MaxVinzens/Cocktail-Mix-Maschine-V2/Doku/Sauber zauber.pdf

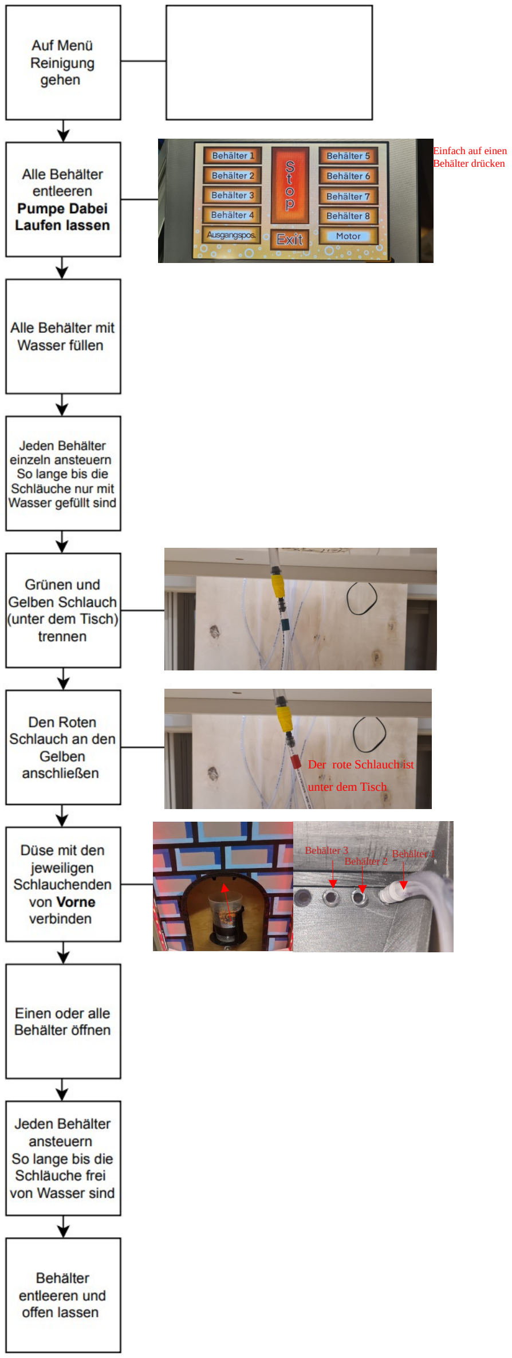
[picture p28: page 1]

Einfach auf einen
Behälter drücken

Behälter 1
Behälter 2

Behälter 3

Der rote Schlauch ist
unter dem Tisch
