MaxVinzens/Cocktail-Mix-Maschine-V2/Konzepte/Saubermachen/Drawing1.pdf

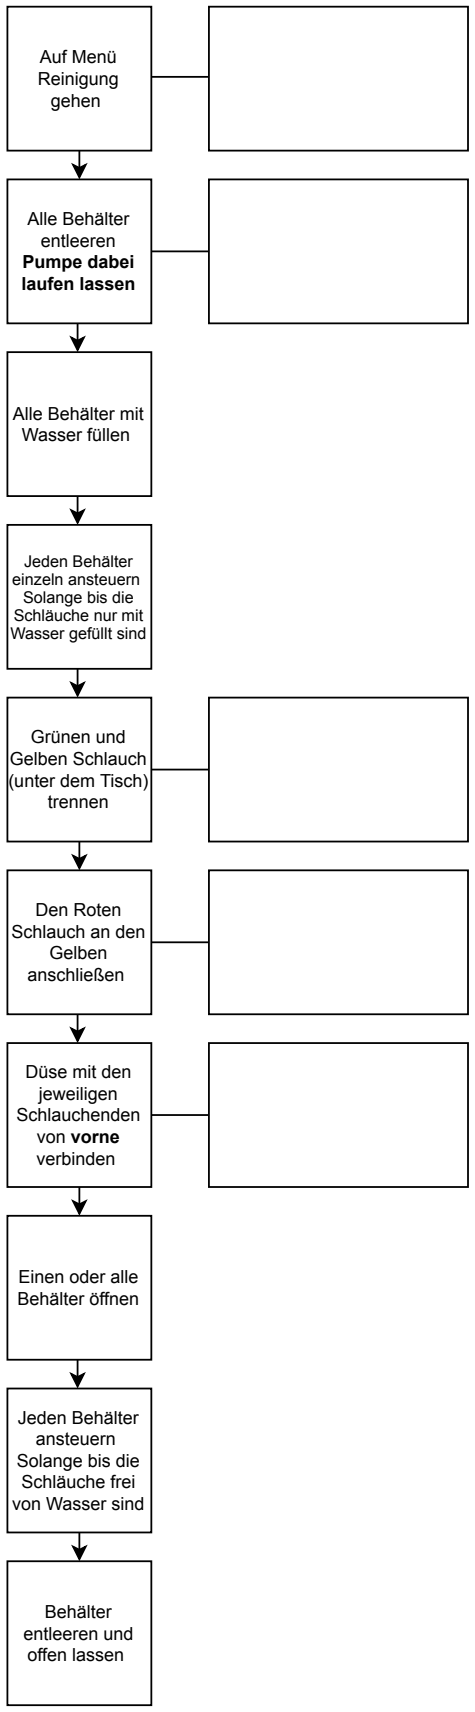
[picture p29: figure]
Auf Menü Reinigung gehen; Alle Behälter entleeren Pumpe dabei laufen lassen; Alle Behälter mit Wasser füllen; Jeden Behälter einzeln ansteuern Solange bis die Schläuche nur mit Wasser gefüllt sind; Grünen und Gelben Schlauch (unter dem Tisch) trennen; Den Roten Schlauch an den Gelben anschließen; Düse mit den jeweiligen Schlauchenden von vorne verbinden; Einen oder alle Behälter öffnen; Jeden Behälter ansteuern Solange bis die Schläuche frei von Wasser sind; Behälter entleeren und offen lassen
