MaxVinzens/Cocktail-Mix-Maschine-V2/Bildschirm Menüs/IMG_2407.jpeg

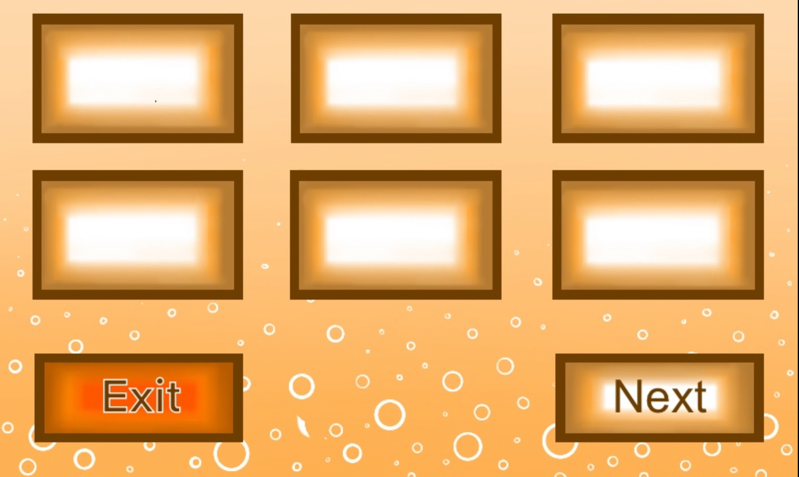
Bildschirm Menüs/IMG_2407.jpeg
