MaxVinzens/Cocktail-Mix-Maschine-V2/Code für SPS/Logical/mappView/Resources/Media/Cocktail.JPG

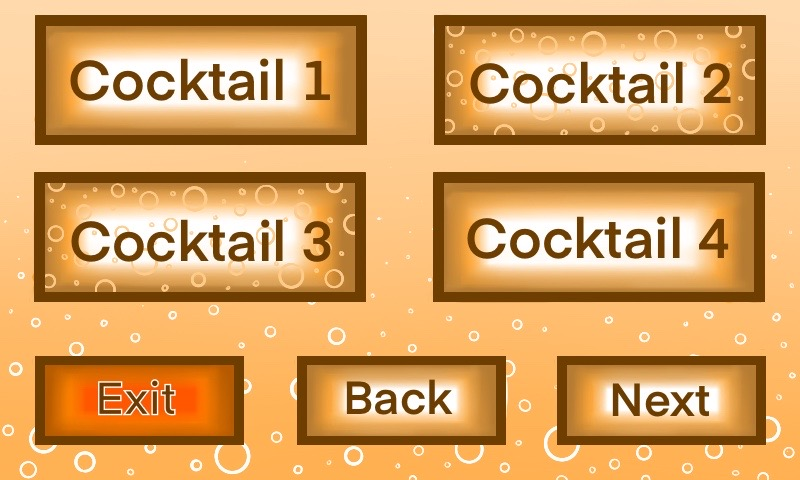
Code für SPS/Logical/mappView/Resources/Media/Cocktail.JPG
