MaxVinzens/Cocktail-Mix-Maschine-V2/Code für SPS/Logical/mappView/Resources/Media/Eis_Groesse.jpg

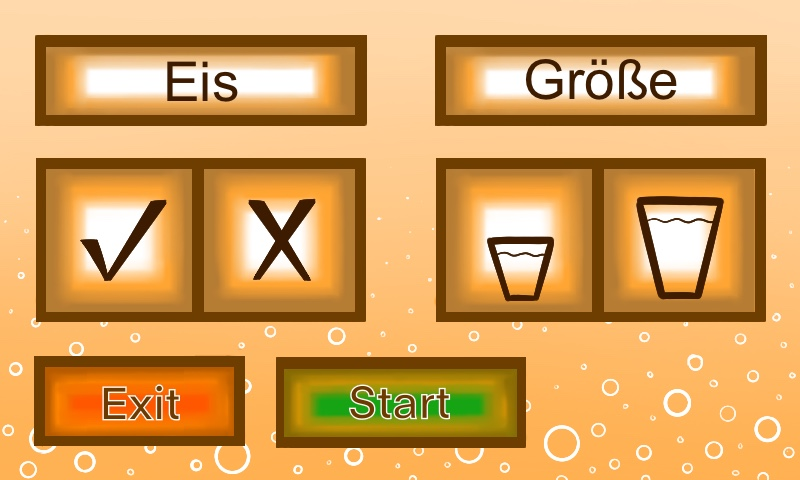
Code für SPS/Logical/mappView/Resources/Media/Eis_Groesse.jpg
