MaxVinzens/Cocktail-Mix-Maschine-V2/Code für SPS/Logical/mappView/Resources/Media/Hauptbildschirm.jpg

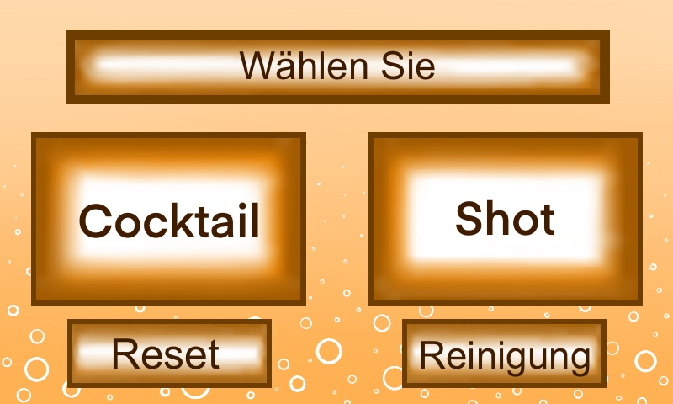
Code für SPS/Logical/mappView/Resources/Media/Hauptbildschirm.jpg
