MaxVinzens/Cocktail-Mix-Maschine-V2/Code für SPS/Logical/mappView/Resources/Media/Reinigung_final.jpg

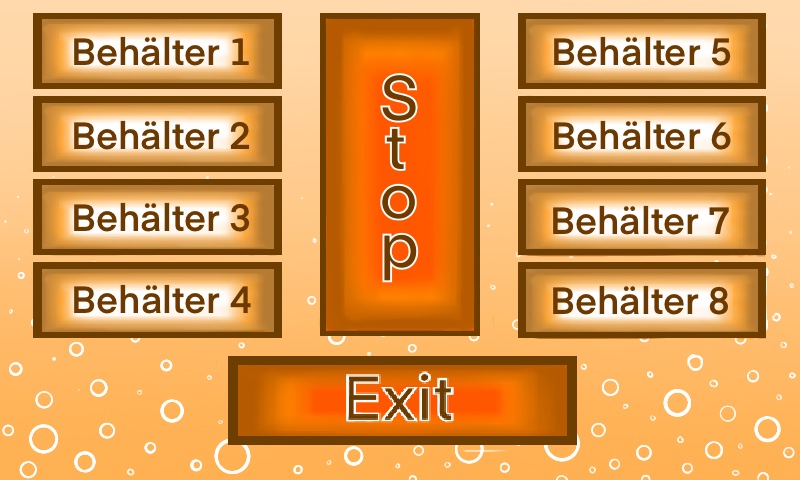
Code für SPS/Logical/mappView/Resources/Media/Reinigung_final.jpg
