MaxVinzens/Cocktail-Mix-Maschine-V2/Code für SPS/Logical/mappView/Resources/Media/Shot.jpg

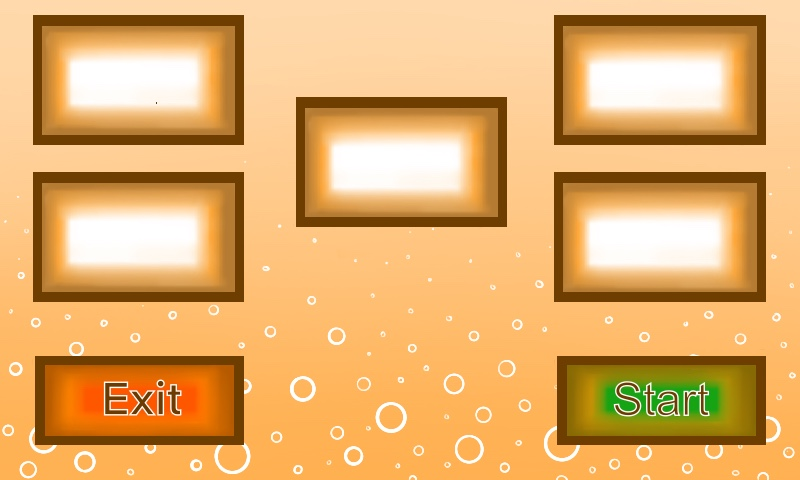
Code für SPS/Logical/mappView/Resources/Media/Shot.jpg
