MaxVinzens/Cocktail-Mix-Maschine-V2/Code für SPS/Logical/mappView/Resources/Media/Startseite.jpg

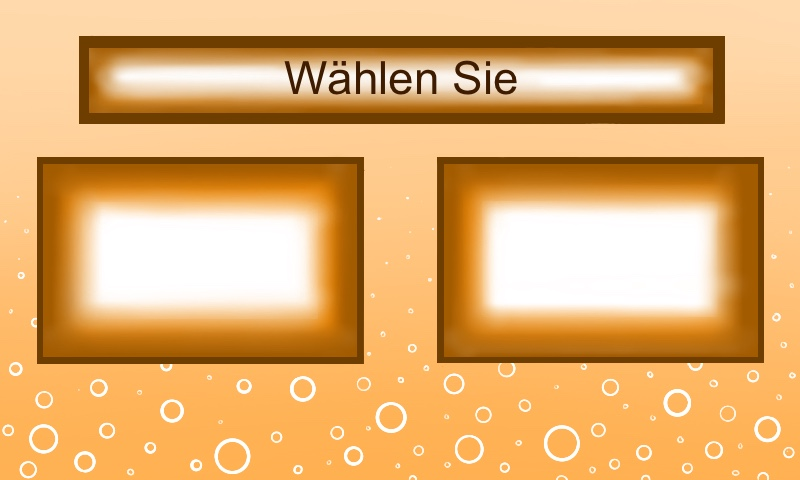
Code für SPS/Logical/mappView/Resources/Media/Startseite.jpg
