MaxVinzens/Cocktail-Mix-Maschine-V2/Code für SPS/Logical/mappView/Resources/Media/Startseite_neu.jpg

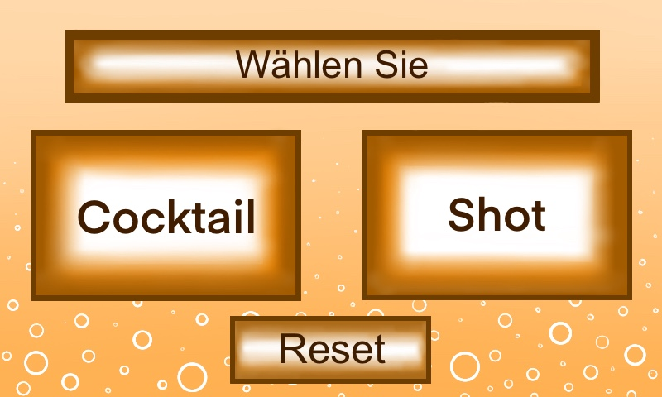
Code für SPS/Logical/mappView/Resources/Media/Startseite_neu.jpg
