MaxVinzens/Cocktail-Mix-Maschine-V2/Doku/Abb.10_Grundskelett_mit_Wägezelle.jpg

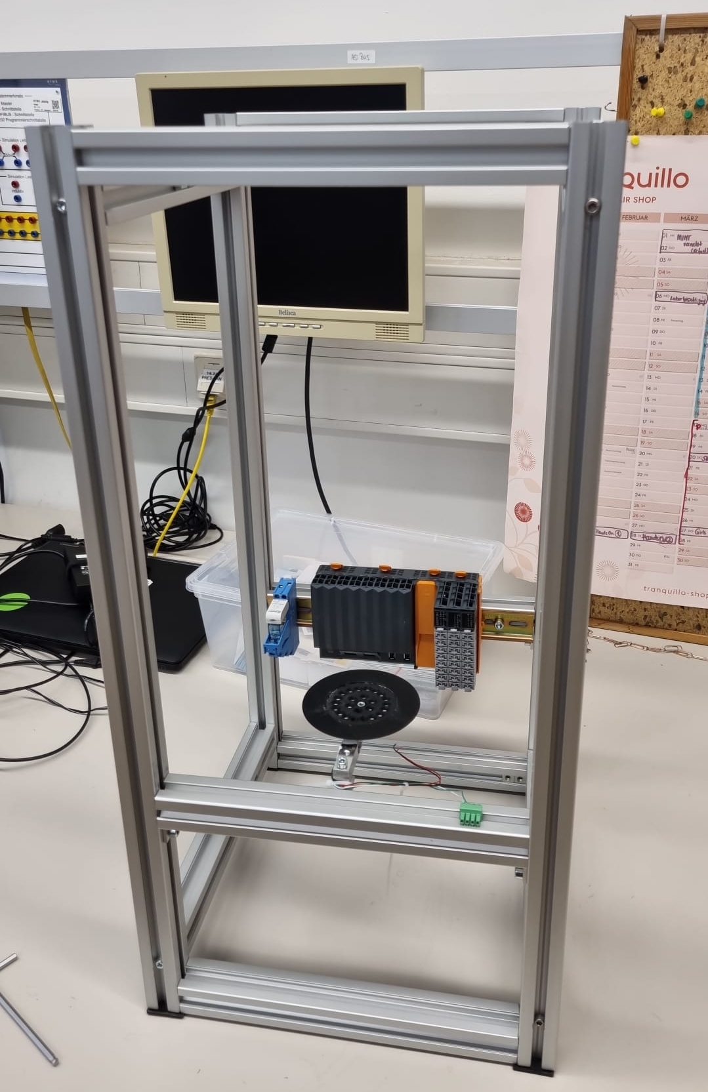
Doku/Abb.10_Grundskelett_mit_Wägezelle.jpg
