MaxVinzens/Cocktail-Mix-Maschine-V2/Fusion/Becherhalter/Für Max (nix ändern)/Schraube.PNG

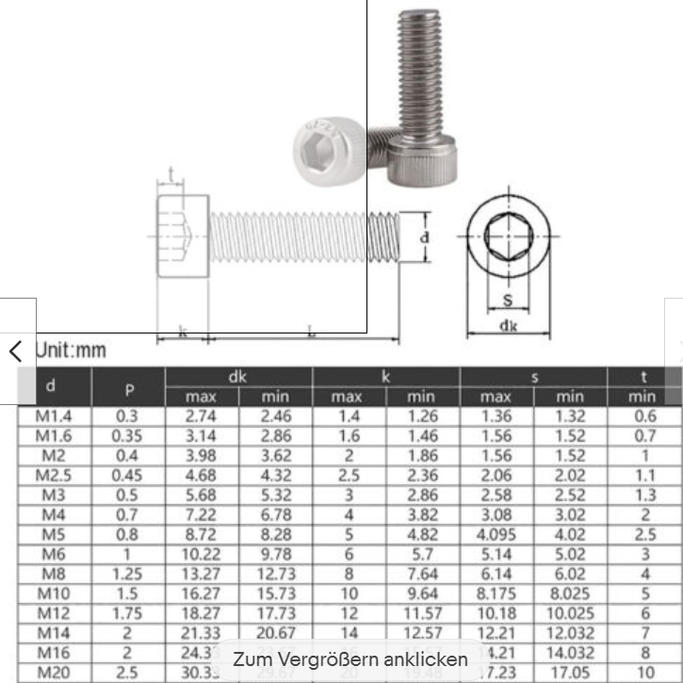
Fusion/Becherhalter/Für Max (nix ändern)/Schraube.PNG
