MaxVinzens/Cocktail-Mix-Maschine-V2/Konzepte/Aussehen/Zeichnung.jpeg

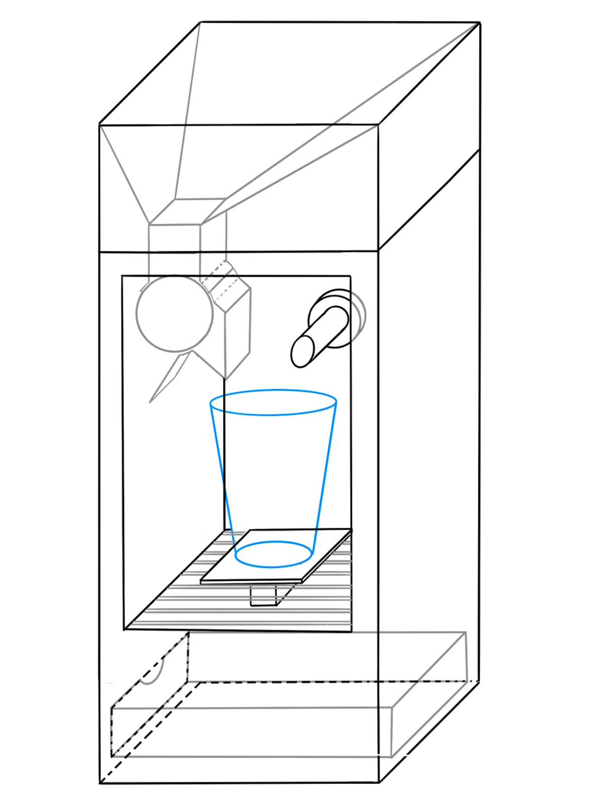
Konzepte/Aussehen/Zeichnung.jpeg
