MaxVinzens/Cocktail-Mix-Maschine-V2/Konzepte/Bildschirm/WhatsApp Image 2023-05-01 at 21.39.04 (1).jpeg

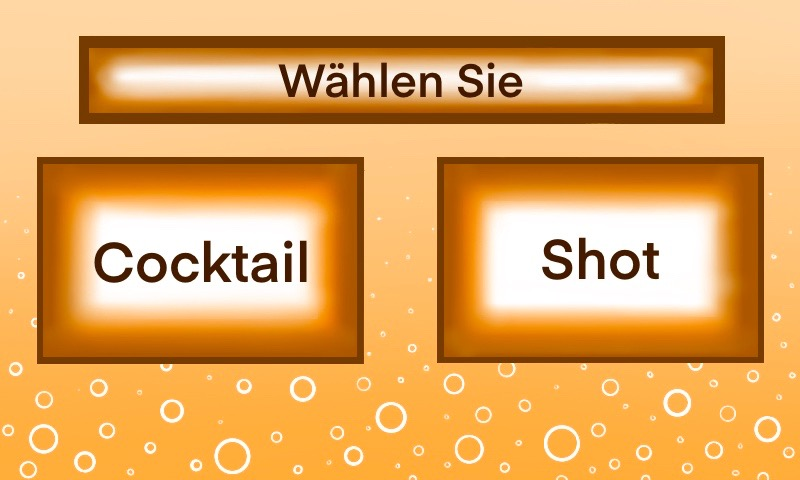
Konzepte/Bildschirm/WhatsApp Image 2023-05-01 at 21.39.04 (1).jpeg
