MaxVinzens/Cocktail-Mix-Maschine-V2/Konzepte/Bildschirm/WhatsApp Image 2023-05-01 at 21.39.05.jpeg

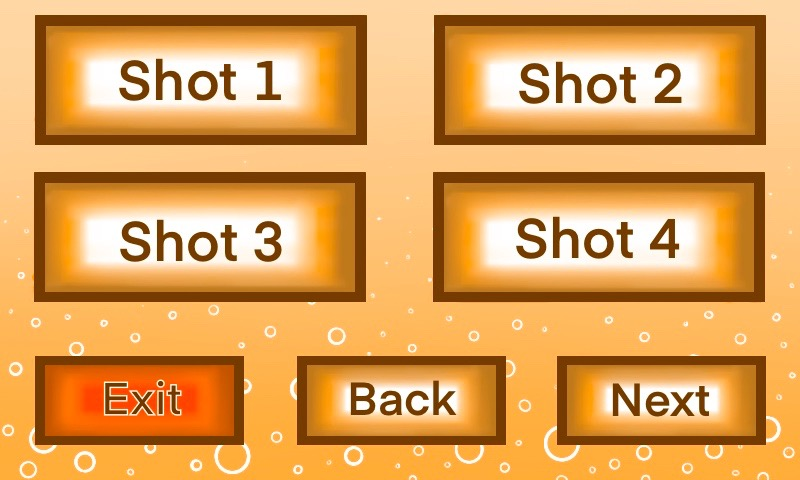
Konzepte/Bildschirm/WhatsApp Image 2023-05-01 at 21.39.05.jpeg
