MaxVinzens/Cocktail-Mix-Maschine-V2/Konzepte/Drinks/drinks1.jpeg

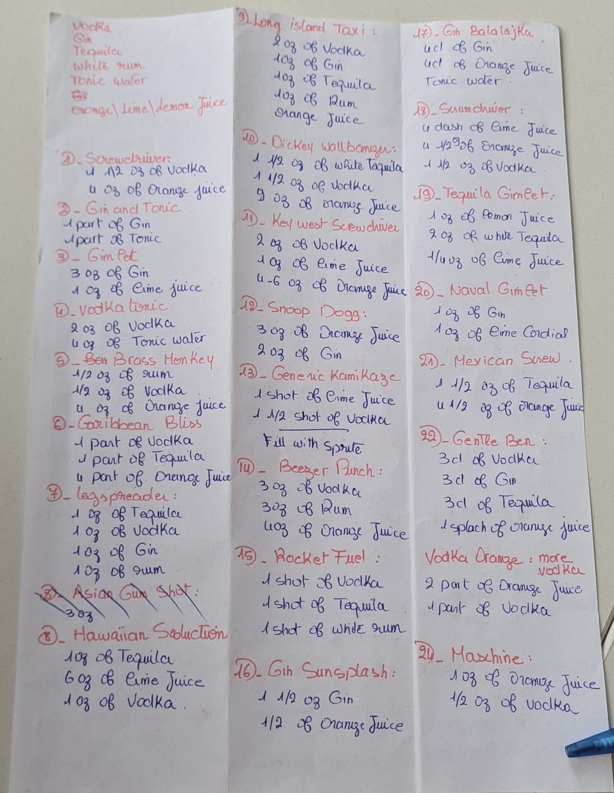
Konzepte/Drinks/drinks1.jpeg
