MaxVinzens/Cocktail-Mix-Maschine-V2/Konzepte/Drinks/Drinks2.jpeg

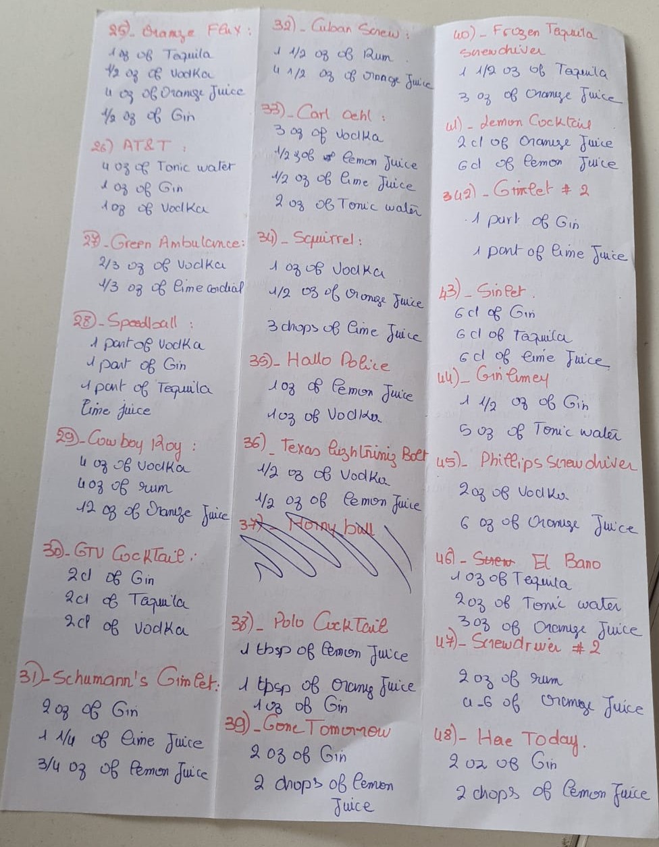
Konzepte/Drinks/Drinks2.jpeg
