MaxVinzens/Cocktail-Mix-Maschine-V2/Reinigung/altes/1.jpg

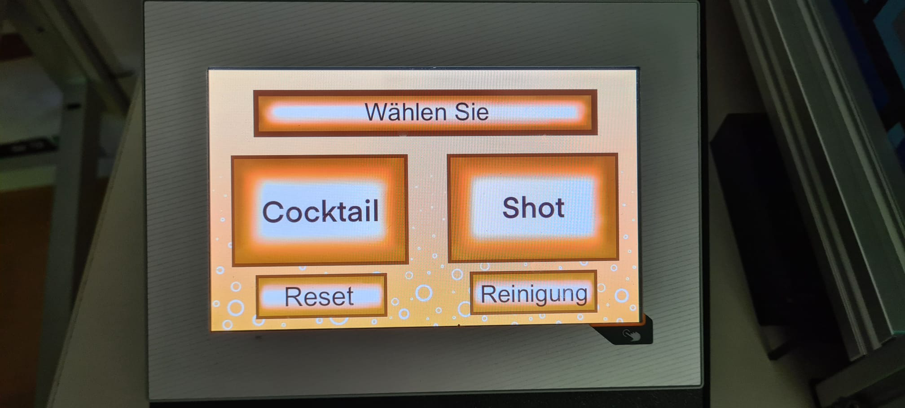
Reinigung/altes/1.jpg
