MaxVinzens/Cocktail-Mix-Maschine-V2/Reinigung/altes/2..jpg

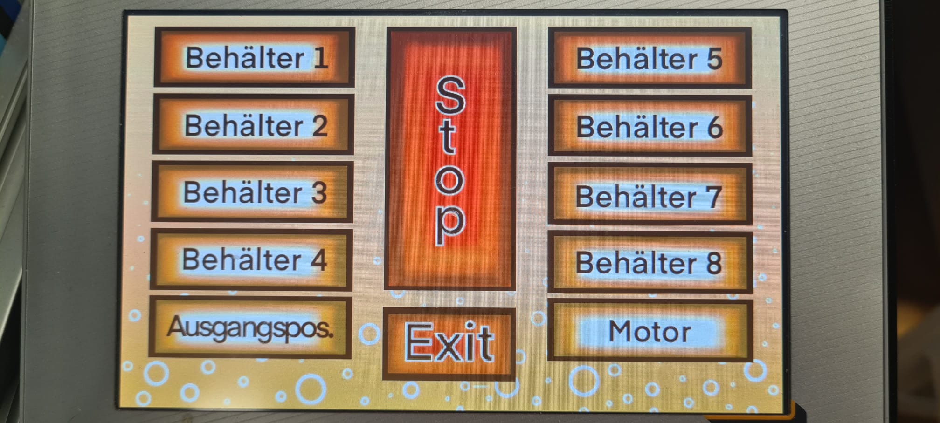
Reinigung/altes/2..jpg
