MaxVinzens/Cocktail-Mix-Maschine-V2/Reinigung/altes/3..jpg

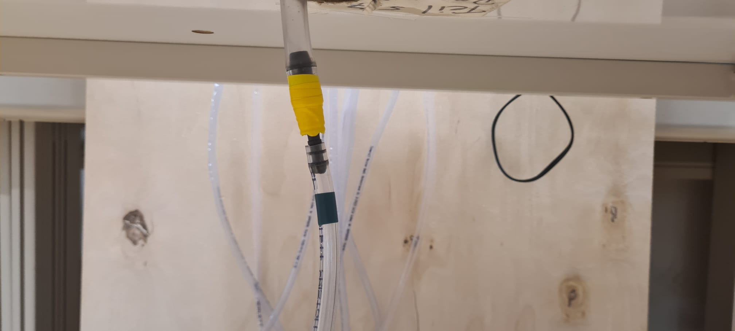
Reinigung/altes/3..jpg
