MaxVinzens/Cocktail-Mix-Maschine-V2/Reinigung/altes/4..jpg

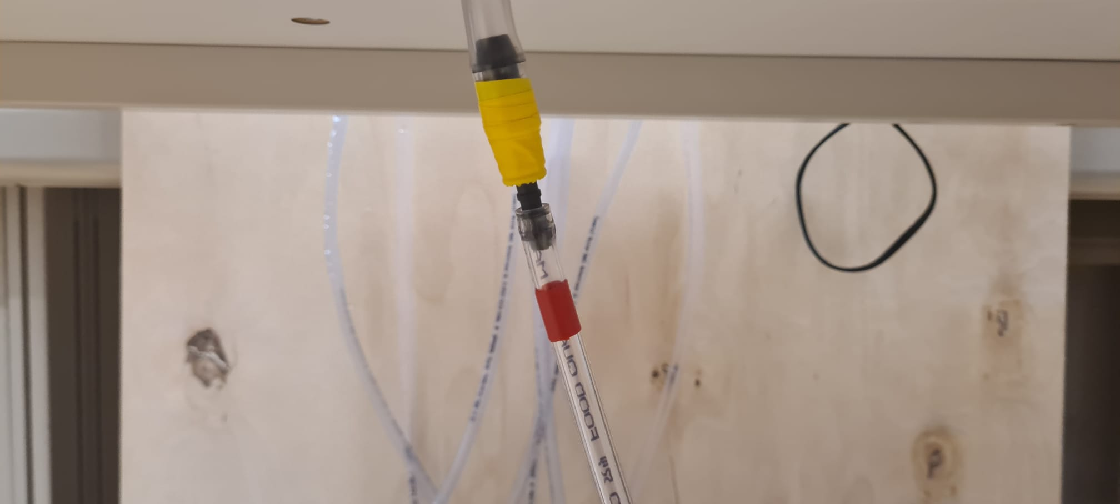
Reinigung/altes/4..jpg
