MaxVinzens/Cocktail-Mix-Maschine-V2/Reinigung/altes/5..jpg

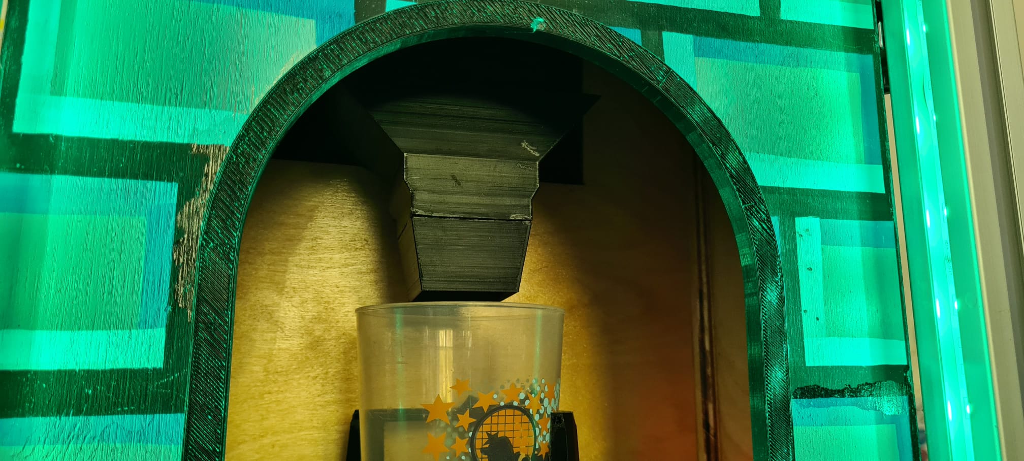
Reinigung/altes/5..jpg
