MaxVinzens/Cocktail-Mix-Maschine-V2/Reinigung/altes/6..jpg

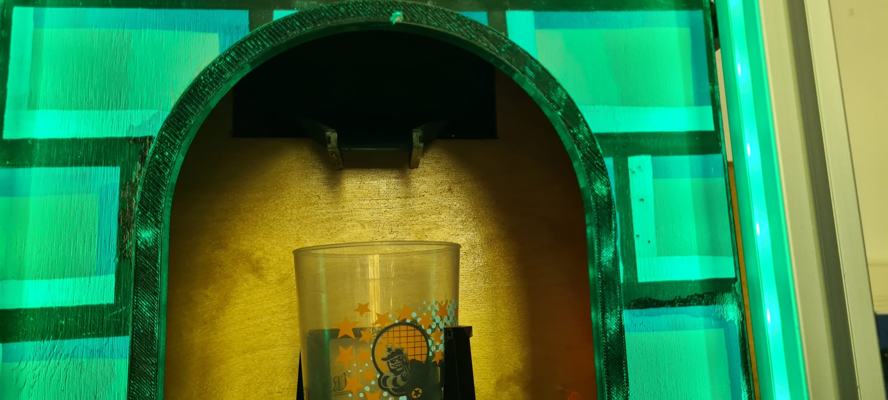
Reinigung/altes/6..jpg
