MaxVinzens/Cocktail-Mix-Maschine-V2/Reinigung/altes/Sauber zauber Bild.PNG

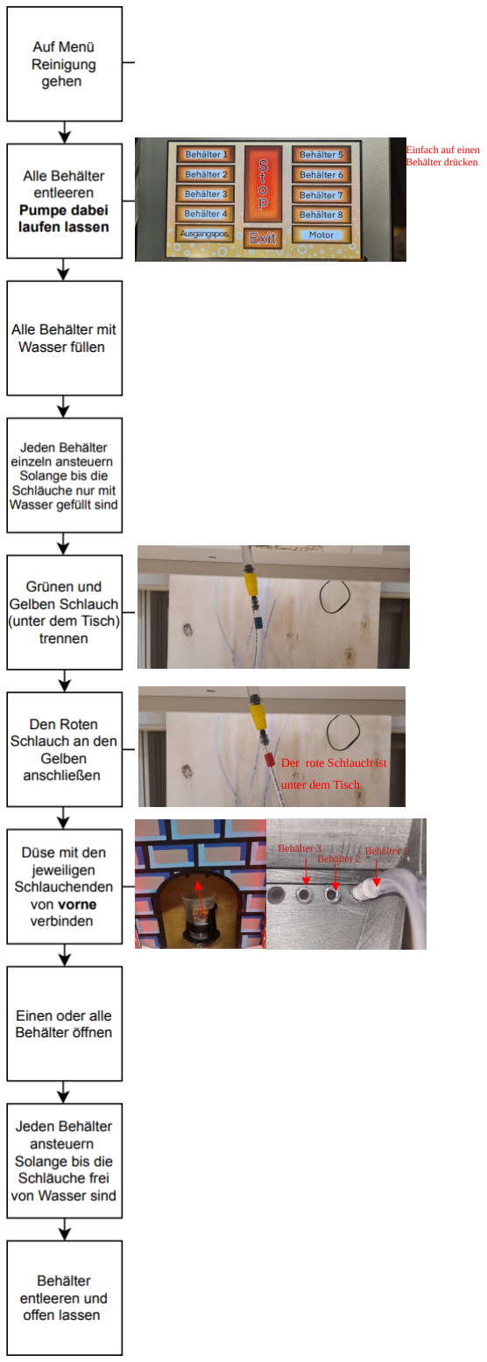
Reinigung/altes/Sauber zauber Bild.PNG
