MaxVinzens/Cocktail-Mix-Maschine-V2/Fusion/Verkleidung/Altes/Abdeckung Profielschiene oben v1.stl

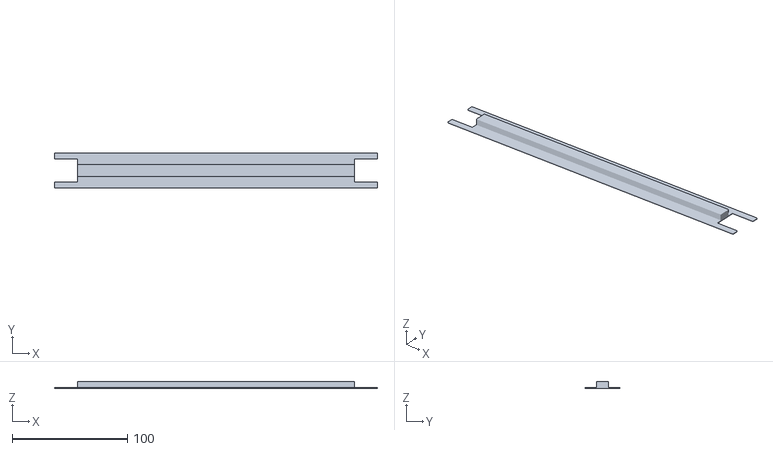
[picture p70: CAD file, 2023-09-12]
Fusion/Verkleidung/Altes/Abdeckung Profielschiene oben v1.stl
280.0 x 30.0 x 6.00
