MaxVinzens/Cocktail-Mix-Maschine-V2/Fusion/Auffangbecken/Halterung Behätler.stl

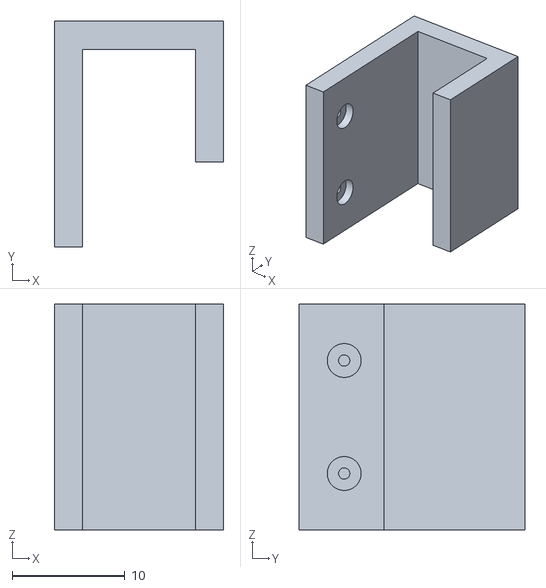
[picture p71: CAD file, 2023-09-09]
Fusion/Auffangbecken/Halterung Behätler.stl
15.0 x 20.0 x 20.0
