MaxVinzens/Cocktail-Mix-Maschine-V2/Fusion/Becherhalter/becherhalter V3 v2.stl

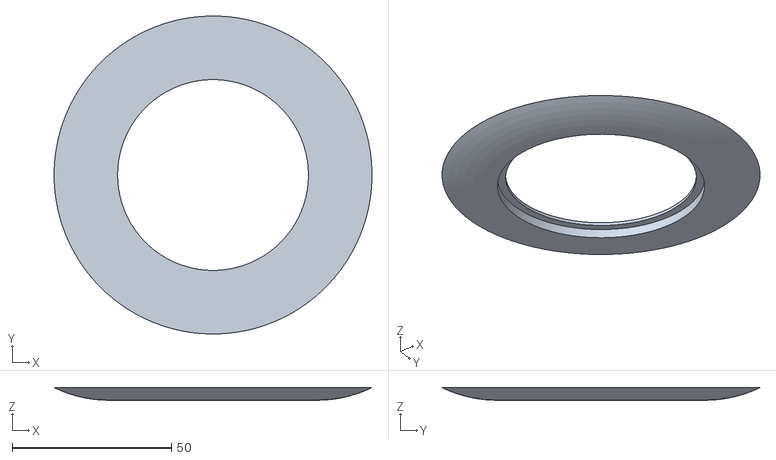
[picture p72: CAD file, 2023-05-09]
Fusion/Becherhalter/becherhalter V3 v2.stl
100.0 x 100.0 x 4.00
