MaxVinzens/Cocktail-Mix-Maschine-V2/Fusion/Eisdosierer/getriebe.FCStd

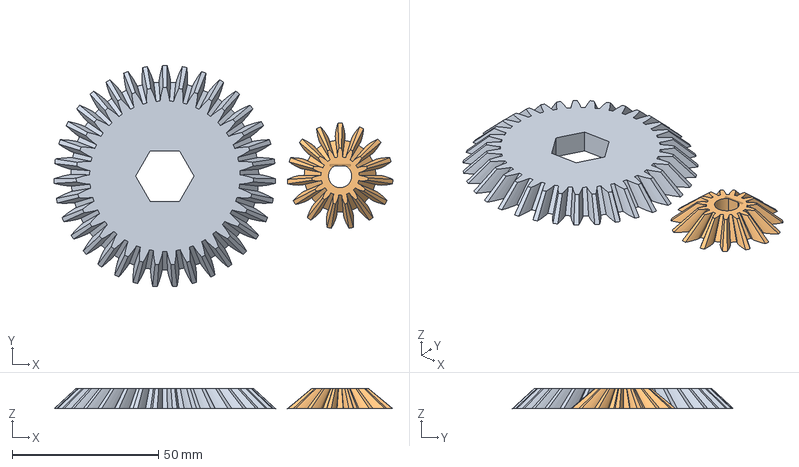
[picture p73: CAD file, 2023-09-13]
Fusion/Eisdosierer/getriebe.FCStd
116.0 x 75.8 x 7.00 mm
Zahnrad Eisdosierer
zahnrad motor
