MaxVinzens/Cocktail-Mix-Maschine-V2/Fusion/Verkleidung/Verkleidung.stl

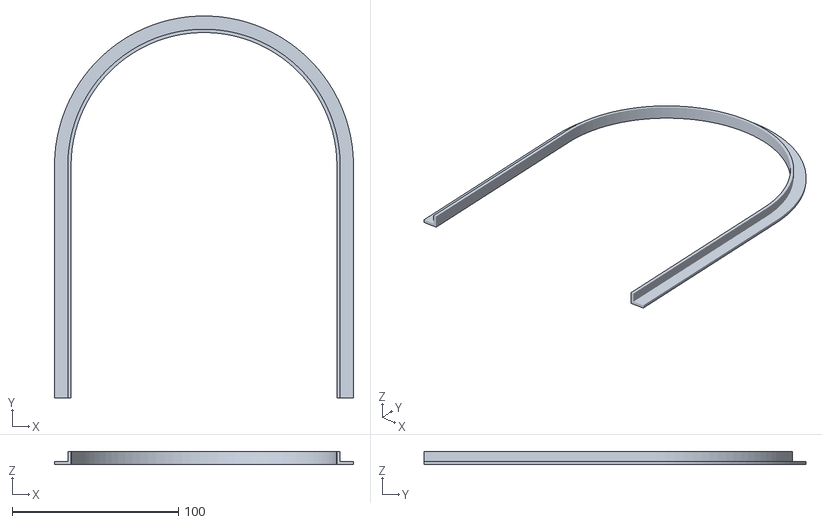
[picture p74: CAD file, 2023-09-10]
Fusion/Verkleidung/Verkleidung.stl
180.0 x 230.0 x 8.00
