MaxVinzens/Cocktail-Mix-Maschine-V2/Fusion/Eisdosierer/Spritzschutz_Schiene-Body.stl

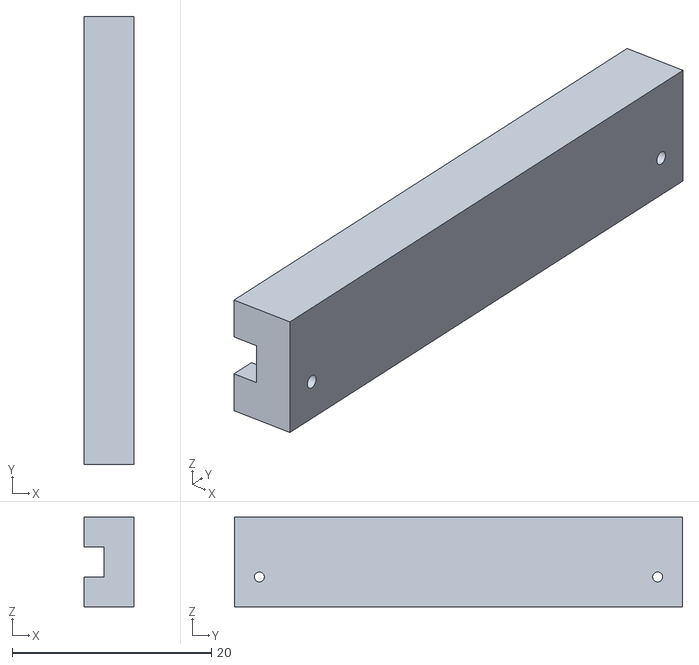
[picture p75: CAD file, 2023-09-13]
Fusion/Eisdosierer/Spritzschutz_Schiene-Body.stl
5.00 x 45.0 x 9.00
