MaxVinzens/Cocktail-Mix-Maschine-V2/Fusion/Eisdosierer/trichter_Ausgang4-Seite1.stl

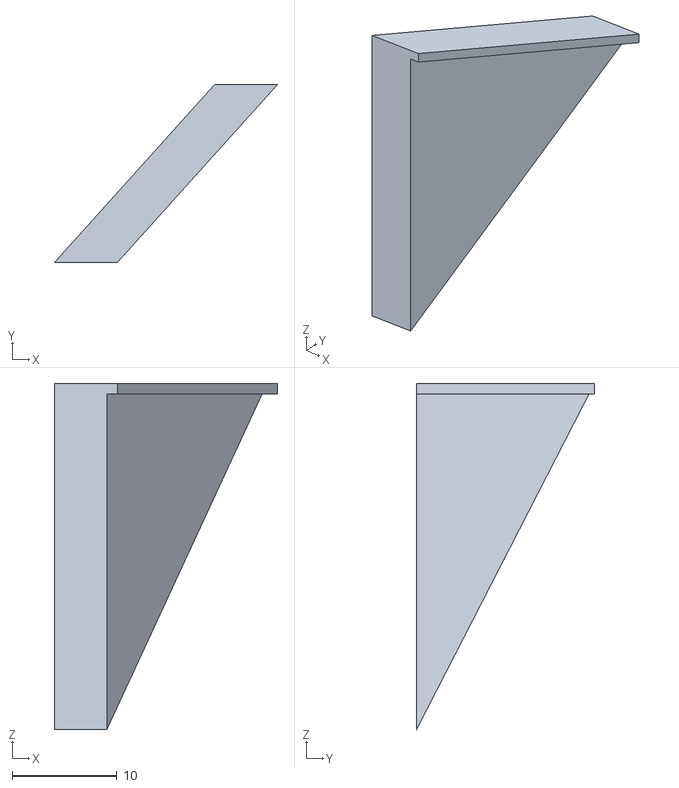
[picture p76: CAD file, 2023-09-13]
Fusion/Eisdosierer/trichter_Ausgang4-Seite1.stl
21.3 x 17.0 x 33.0
