MaxVinzens/Cocktail-Mix-Maschine-V2/Fusion/Eisdosierer/Eisdosierer_walze2.FCStd

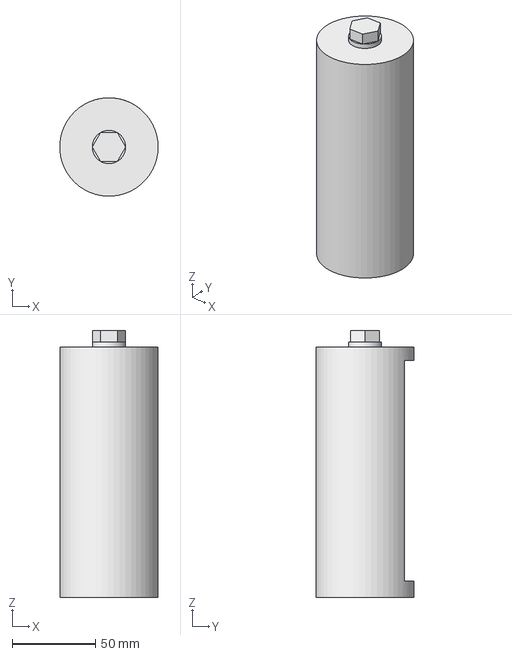
[picture p77: CAD file, 2023-09-13]
Fusion/Eisdosierer/Eisdosierer_walze2.FCStd
58.9 x 59.0 x 160.0 mm
