MaxVinzens/Cocktail-Mix-Maschine-V2/Fusion/Eisdosierer/trichter_Ausgang4.FCStd

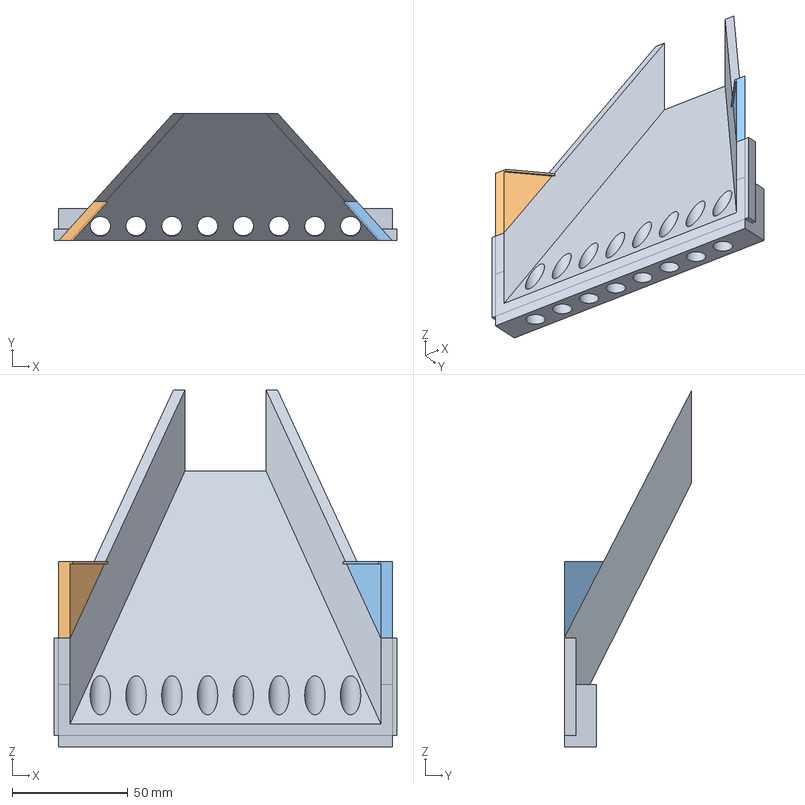
[picture p78: CAD file, 2023-09-13]
Fusion/Eisdosierer/trichter_Ausgang4.FCStd
148.0 x 55.0 x 154.0 mm
Seite1
Seite2
