MaxVinzens/Cocktail-Mix-Maschine-V2/Fusion/Eisdosierer/Spritzschutz-Teil2.stl

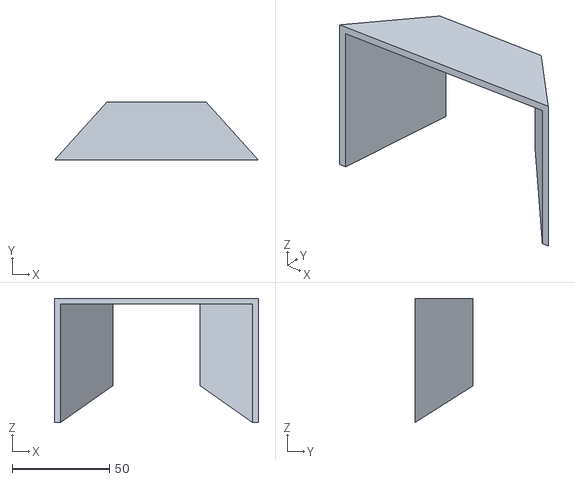
[picture p79: CAD file, 2023-09-13]
Fusion/Eisdosierer/Spritzschutz-Teil2.stl
105.0 x 30.0 x 64.0
