MaxVinzens/Cocktail-Mix-Maschine-V2/Fusion/Eisdosierer/Platte_mitloch.FCStd

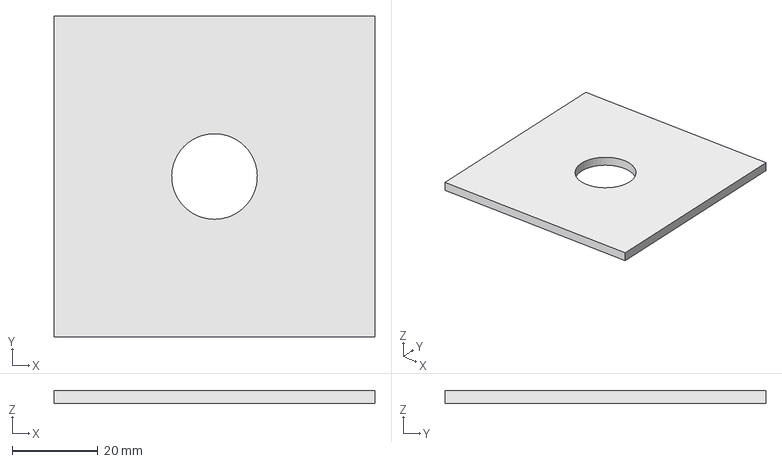
[picture p80: CAD file, 2023-09-13]
Fusion/Eisdosierer/Platte_mitloch.FCStd
75.0 x 75.0 x 3.00 mm
