MaxVinzens/Cocktail-Mix-Maschine-V2/Fusion/Eisdosierer/Eisdosierer1.FCStd

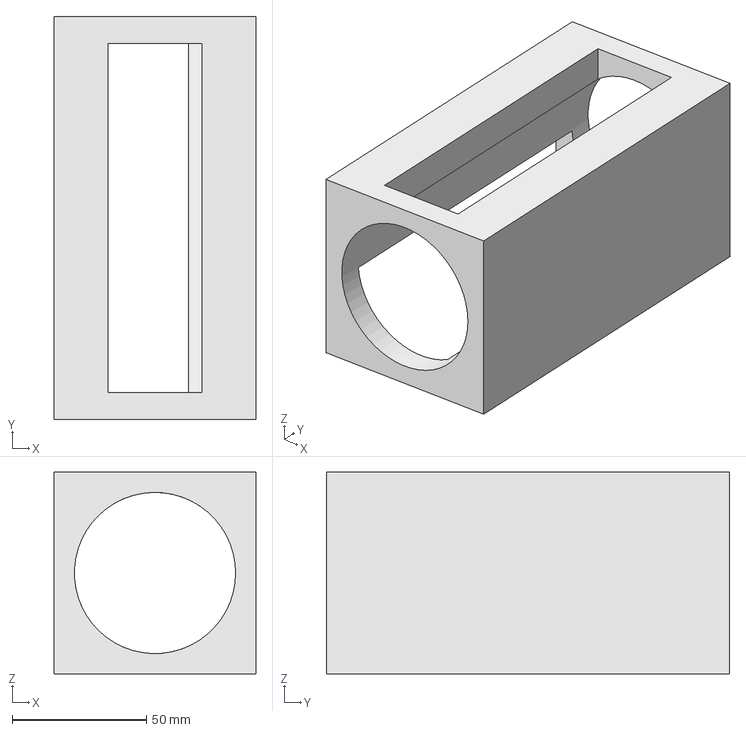
[picture p81: CAD file, 2023-09-13]
Fusion/Eisdosierer/Eisdosierer1.FCStd
75.0 x 150.0 x 75.0 mm
