MaxVinzens/Cocktail-Mix-Maschine-V2/Fusion/Eisdosierer/Spritzschutz.FCStd

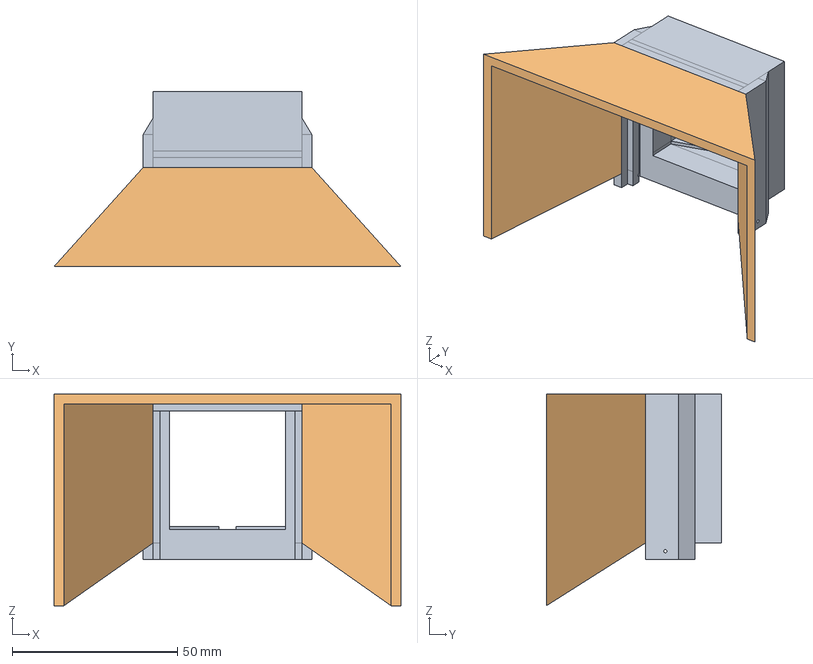
[picture p82: CAD file, 2023-09-13]
Fusion/Eisdosierer/Spritzschutz.FCStd
105.0 x 53.0 x 64.0 mm
Teil1
Teil2
