MaxVinzens/Cocktail-Mix-Maschine-V2/Fusion/Eisdosierer/Trichter_Eingang_neu_teil1.FCStd

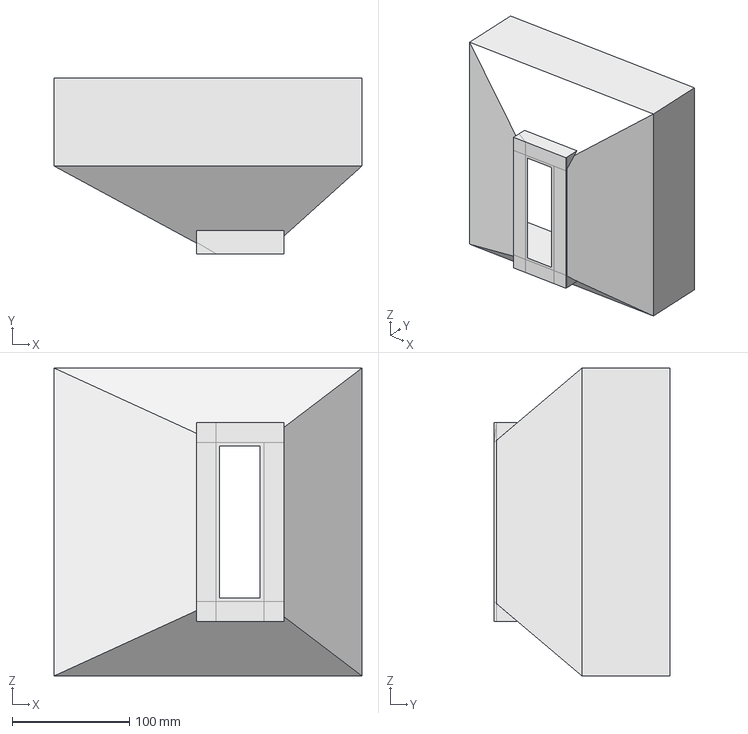
[picture p83: CAD file, 2023-09-13]
Fusion/Eisdosierer/Trichter_Eingang_neu_teil1.FCStd
263.0 x 150.0 x 263.0 mm
