MaxVinzens/Cocktail-Mix-Maschine-V2/Fusion/Eisdosierer/trichter_Ausgang4-Body.stl

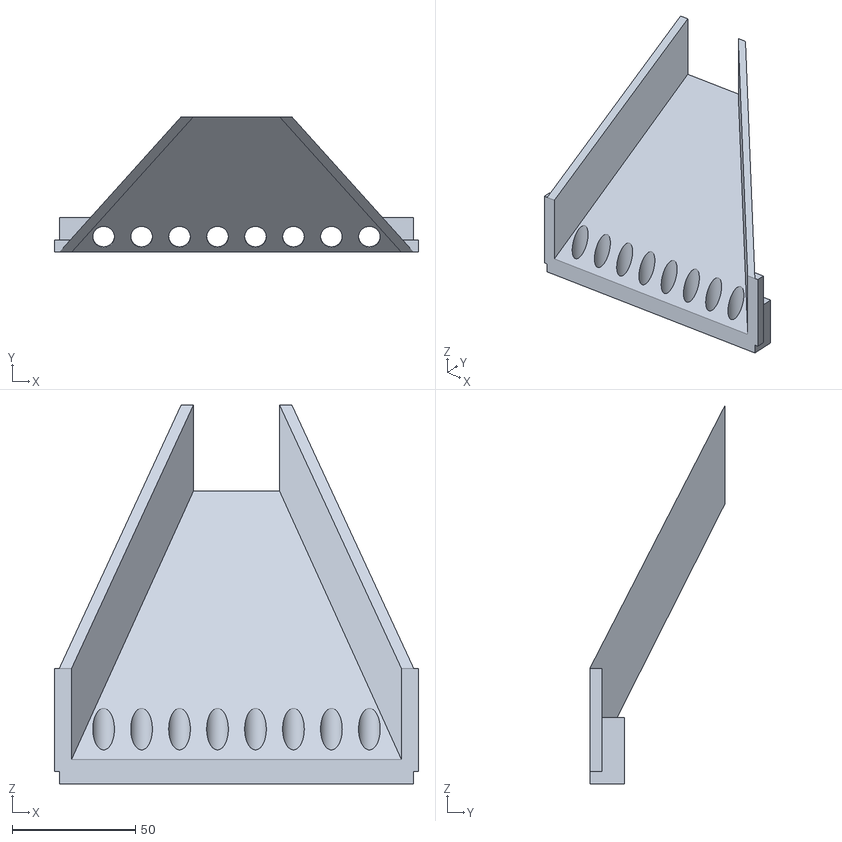
[picture p84: CAD file, 2023-08-09]
Fusion/Eisdosierer/trichter_Ausgang4-Body.stl
148.0 x 55.0 x 154.0
