MaxVinzens/Cocktail-Mix-Maschine-V2/Fusion/Eisdosierer/Entlagenschalter_Halter.FCStd

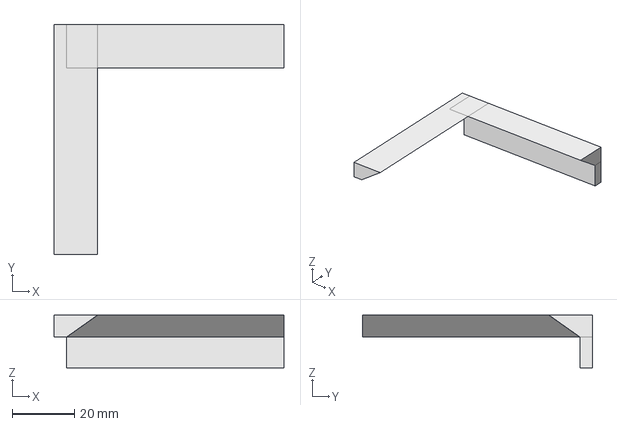
[picture p85: CAD file, 2023-06-29]
Fusion/Eisdosierer/Entlagenschalter_Halter.FCStd
74.0 x 74.0 x 17.0 mm
