MaxVinzens/Cocktail-Mix-Maschine-V2/Fusion/Eisdosierer/getriebe-Zahnrad Eisdosierer.stl

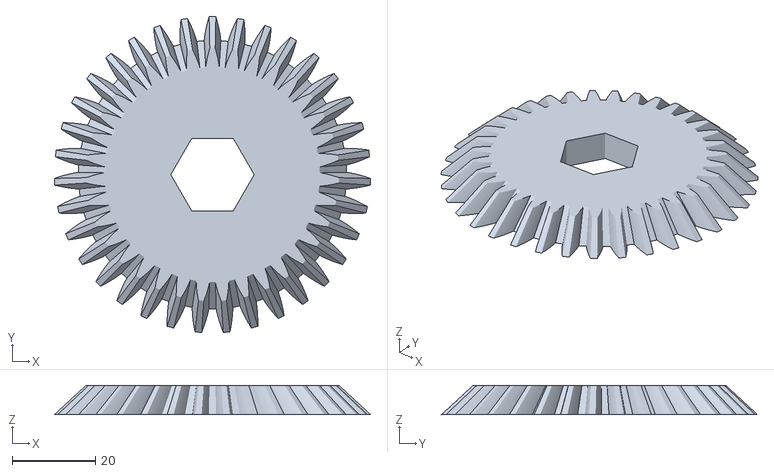
[picture p86: CAD file, 2023-06-15]
Fusion/Eisdosierer/getriebe-Zahnrad Eisdosierer.stl
75.9 x 75.8 x 7.00
