MaxVinzens/Cocktail-Mix-Maschine-V2/Fusion/Eisdosierer/Eisdosierer_walze2-Body.stl

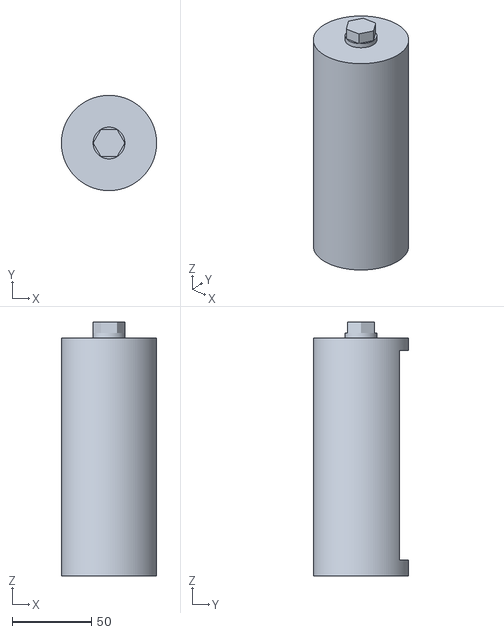
[picture p87: CAD file, 2023-06-15]
Fusion/Eisdosierer/Eisdosierer_walze2-Body.stl
60.0 x 60.0 x 160.0
