MaxVinzens/Cocktail-Mix-Maschine-V2/Fusion/Eisdosierer/getriebe-zahnrad motor.stl

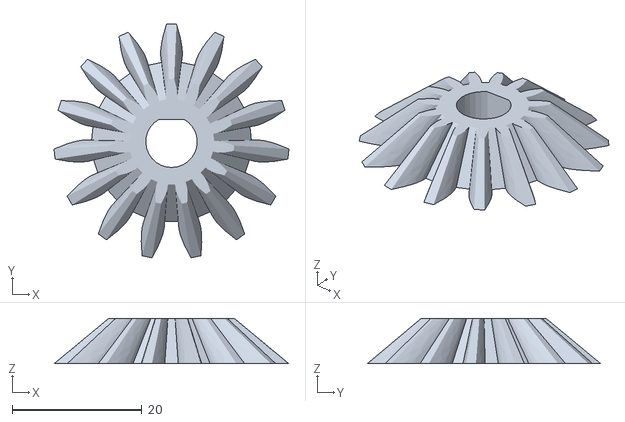
[picture p88: CAD file, 2023-06-15]
Fusion/Eisdosierer/getriebe-zahnrad motor.stl
36.2 x 36.0 x 7.00
