MaxVinzens/Cocktail-Mix-Maschine-V2/Doku/DI AI (V2).pdf

1 | 2 | 3 | 4 | 5 | 6 | 7 | 8 | 9

A

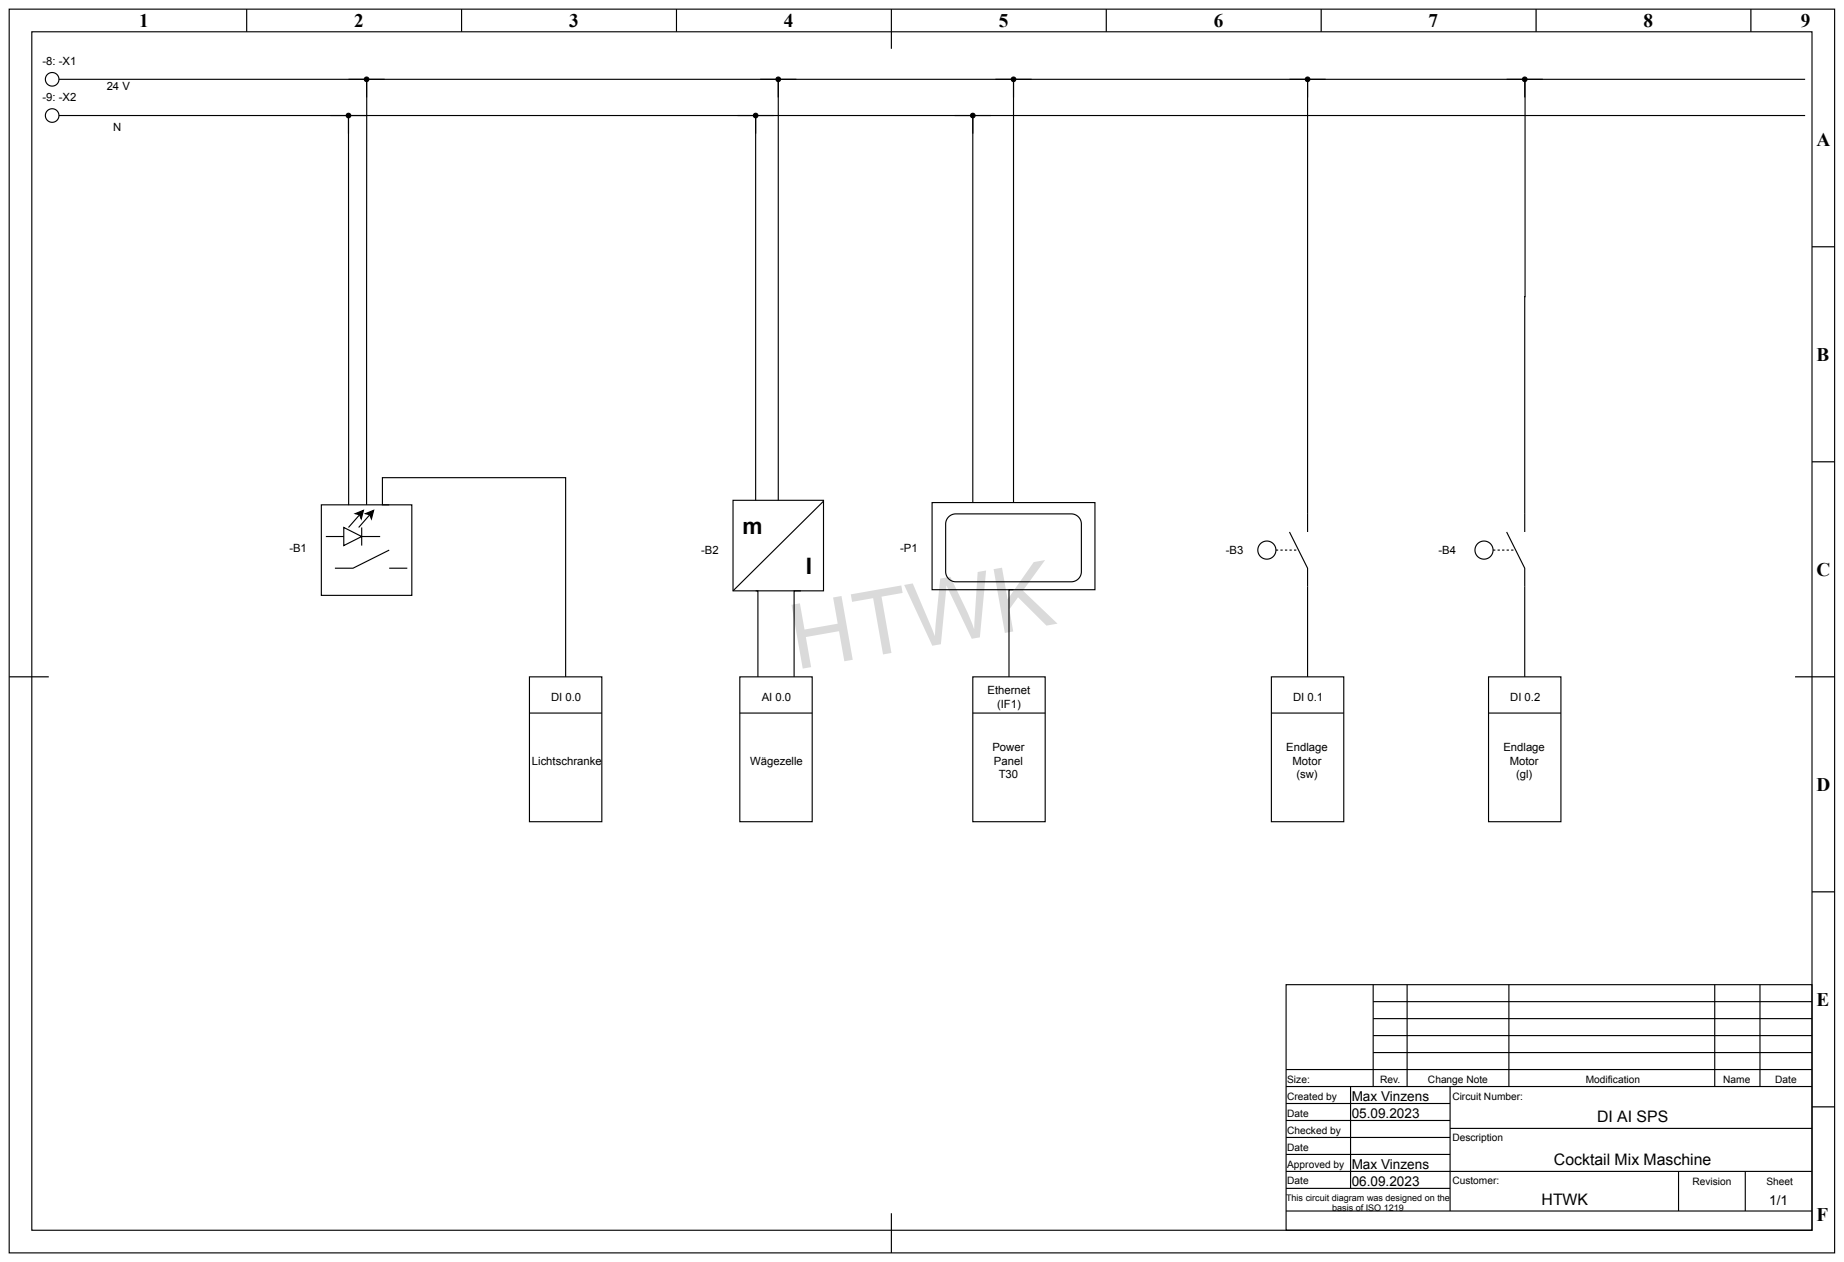
[picture p102: page 1]
Size:; Rev.; Change Note; Modification; Name; Date; Customer:; Description; Circuit Number:; Revision; Sheet; HTWK; Max Vinzens; Lichtschranke; Wägezelle; Ethernet (IF1); Power Panel T30; Endlage Motor (sw); Endlage Motor (gl)

Created by
Date
Checked by
Approved by
This circuit diagram was designed on the

DI AI SPS

Cocktail Mix Maschine

basis of ISO 1219
