MaxVinzens/Cocktail-Mix-Maschine-V2/Doku/DO AO SPS (V2).pdf

1 | 2 | 3 | 4 | 5 | 6 | 7 | 8 | 9

A

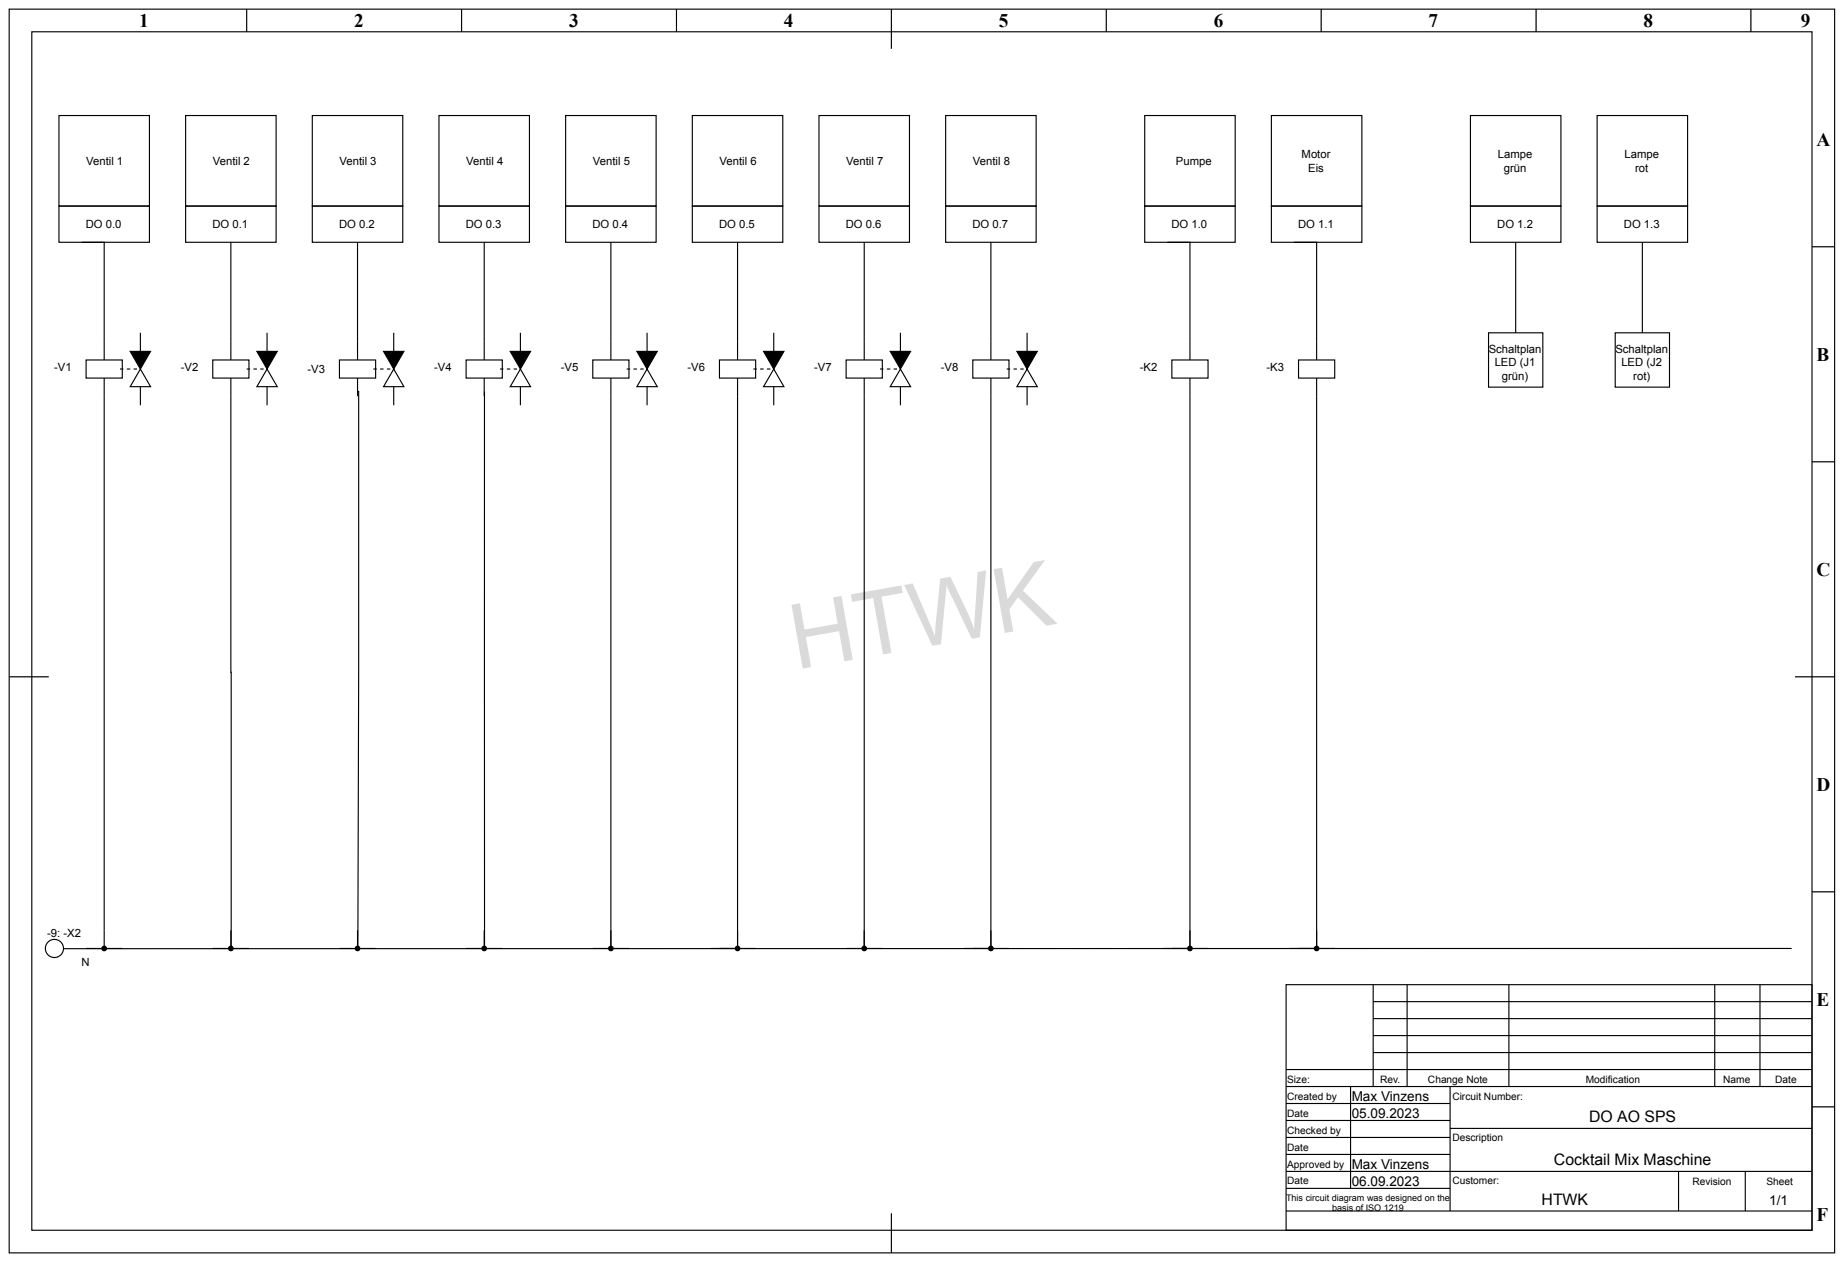
[picture p103: page 1]
Size:; Rev.; Change Note; Modification; Name; Date; Customer:; Description; Circuit Number:; Revision; Sheet; HTWK; Max Vinzens; Schaltplan LED (J1 grün); Schaltplan LED (J2 rot); Ventil 1; Ventil 2; Ventil 3; Ventil 4; Ventil 5; Ventil 6; Ventil 7; Ventil 8; Pumpe; Motor; Eis; Lampe rot; Lampe grün

Created by
Date
Checked by
Approved by
This circuit diagram was designed on the

DO AO SPS

Cocktail Mix Maschine

basis of ISO 1219
