MaxVinzens/Cocktail-Mix-Maschine-V2/Doku/LEDs (V2).pdf

1 | 2 | 3 | 4 | 5 | 6 | 7 | 8 | 9

A

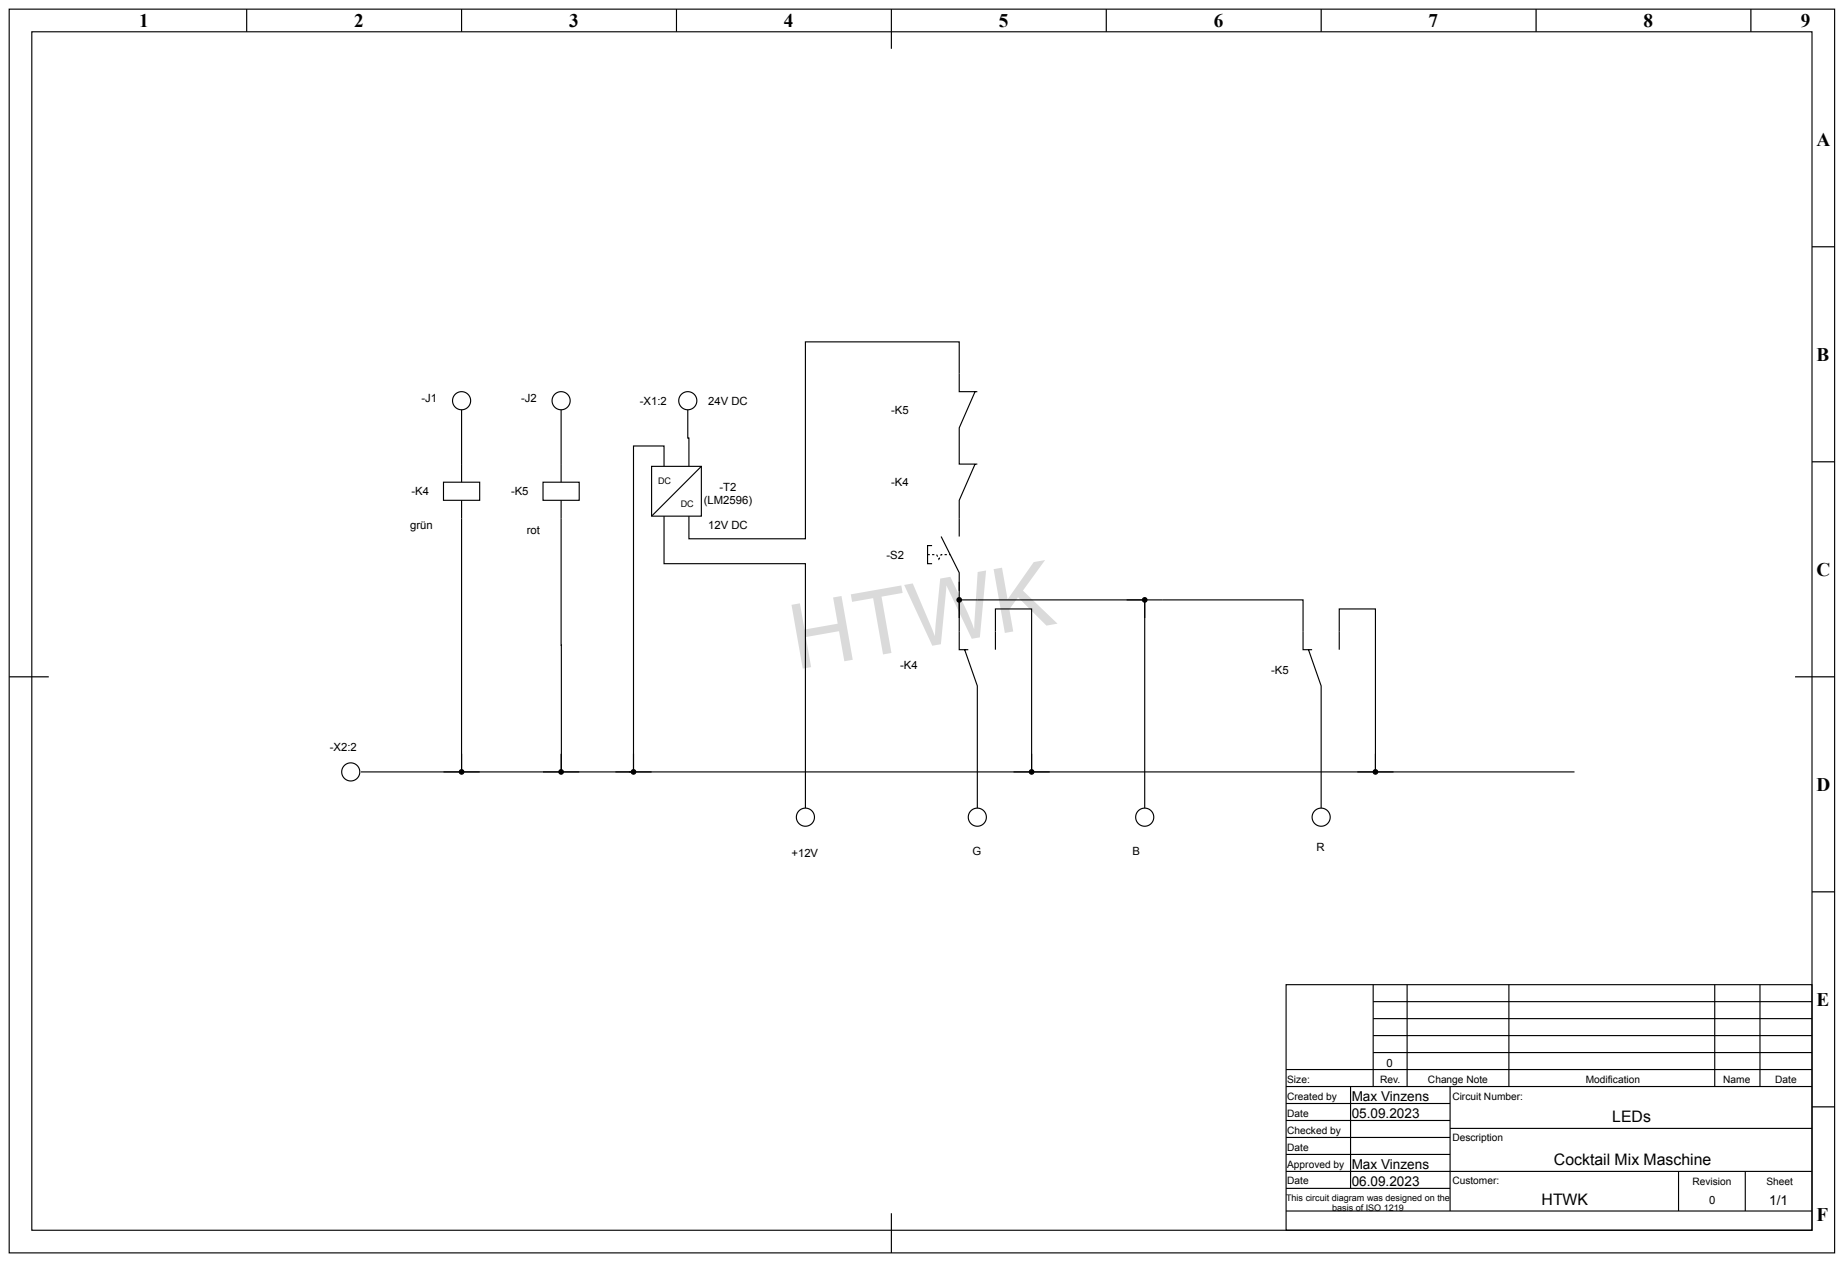
[picture p104: page 1]
Size:; Rev.; Change Note; Modification; Name; Date; Customer:; Description; Circuit Number:; Revision; Sheet; HTWK; Max Vinzens; LEDs; grün; rot

Created by
Date
Checked by
Approved by
This circuit diagram was designed on the

Cocktail Mix Maschine

basis of ISO 1219
