MaxVinzens/Cocktail-Mix-Maschine-V2/Doku/Pneumatik (Version2).pdf

1 | 2 | 3 | 4 | 5 | 6 | 7 | 8 | 9

A

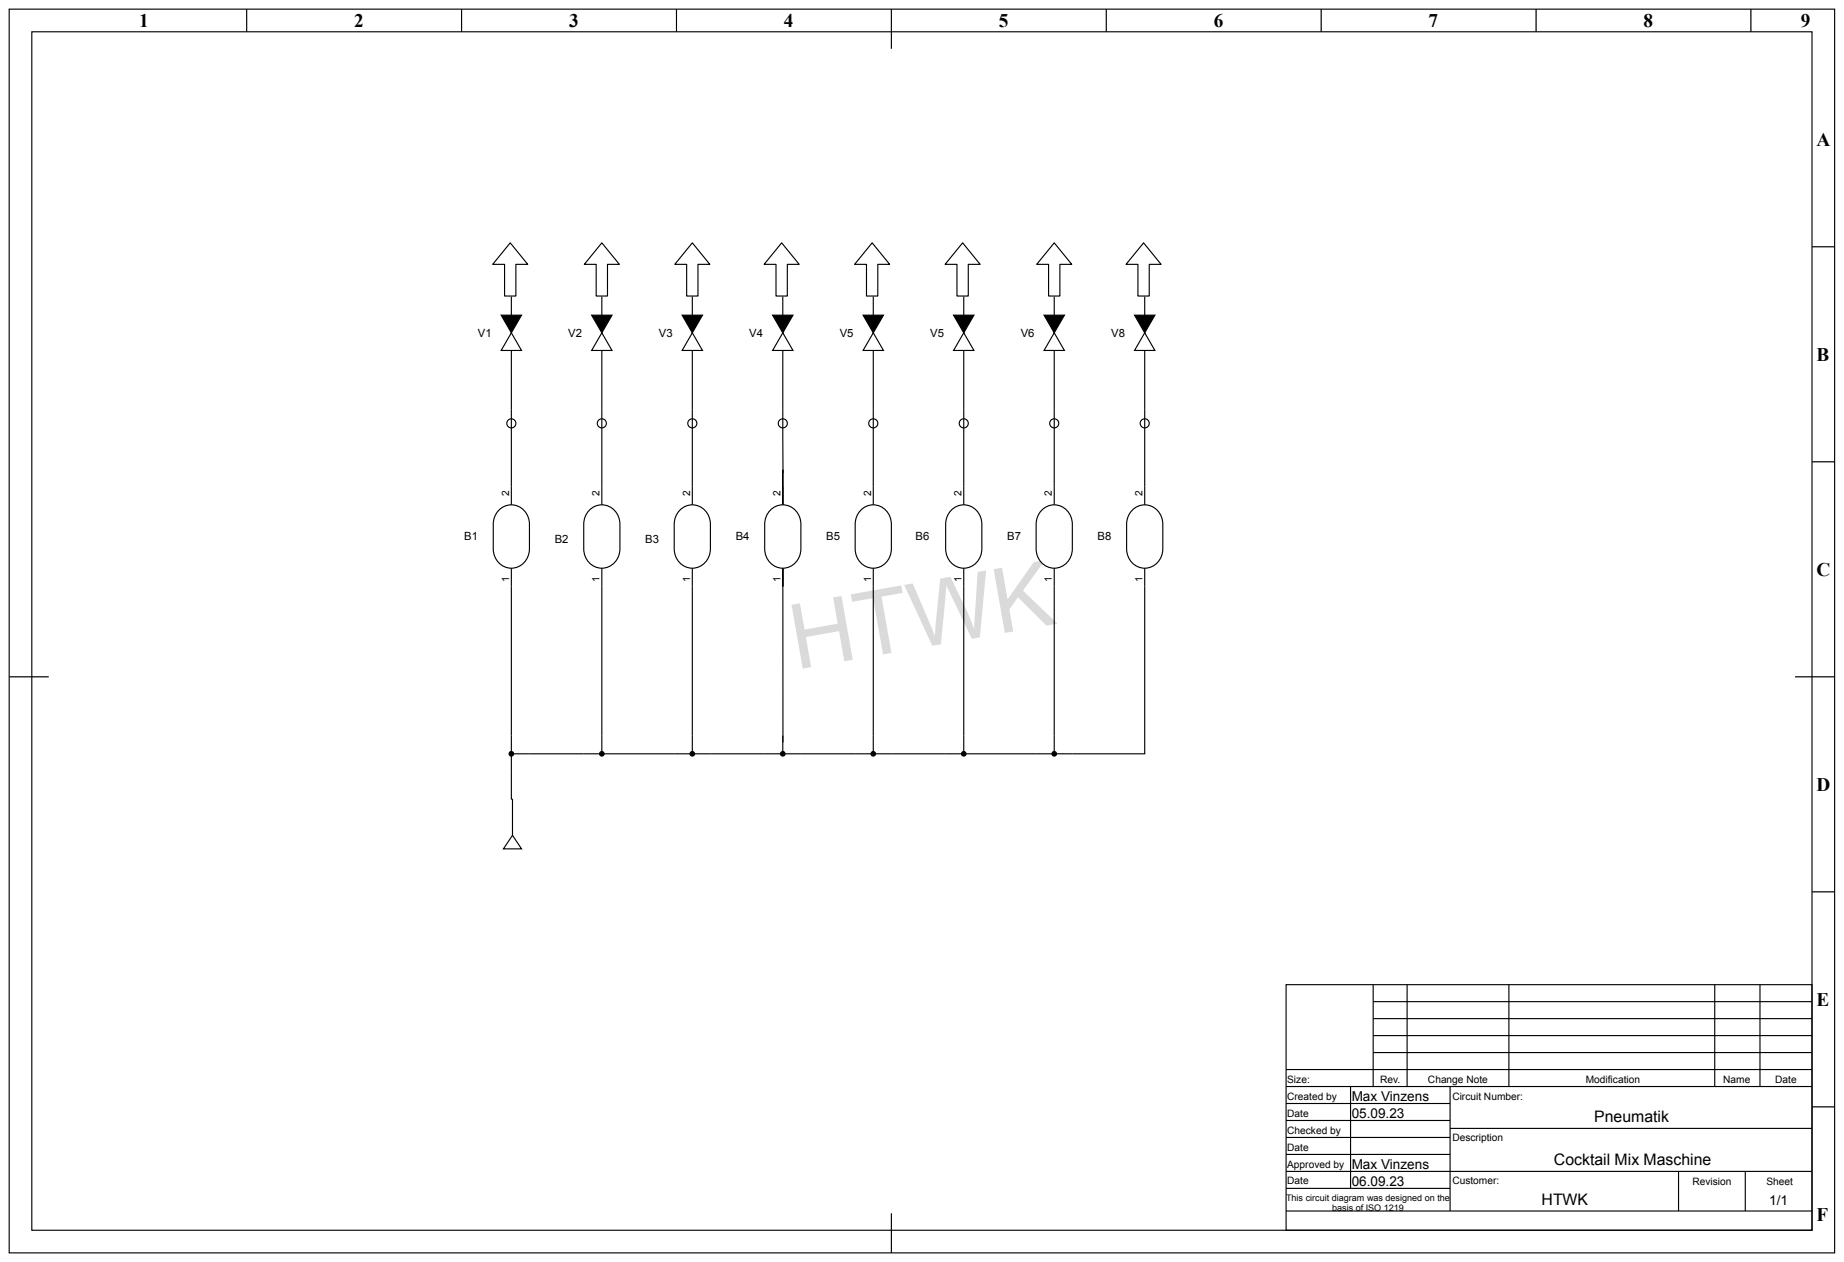
[picture p105: page 1]
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

Created by
Date
Checked by
Approved by
This circuit diagram was designed on the

Cocktail Mix Maschine

basis of ISO 1219
