MaxVinzens/Cocktail-Mix-Maschine-V2/Fusion/Eisdosierer/Tech_Zeichnung_Eisdosierer.pdf

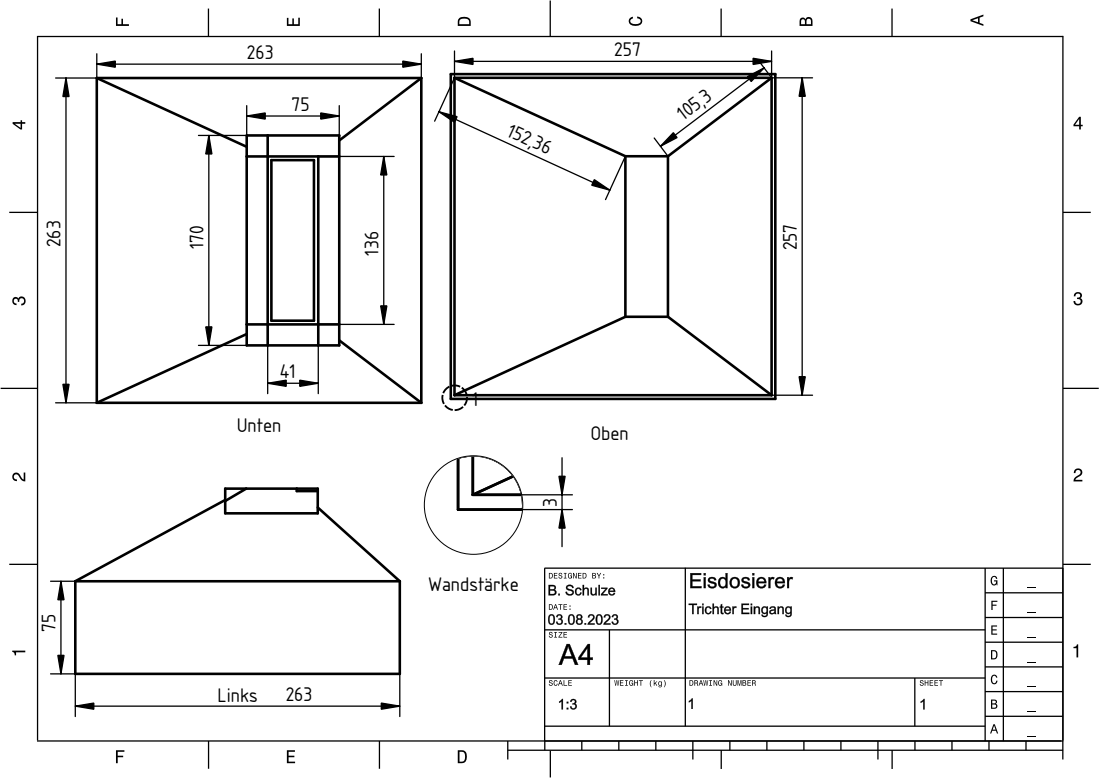
[picture p106: page 1]
Unten; Links; Oben; Wandstärke

n 150

e 150

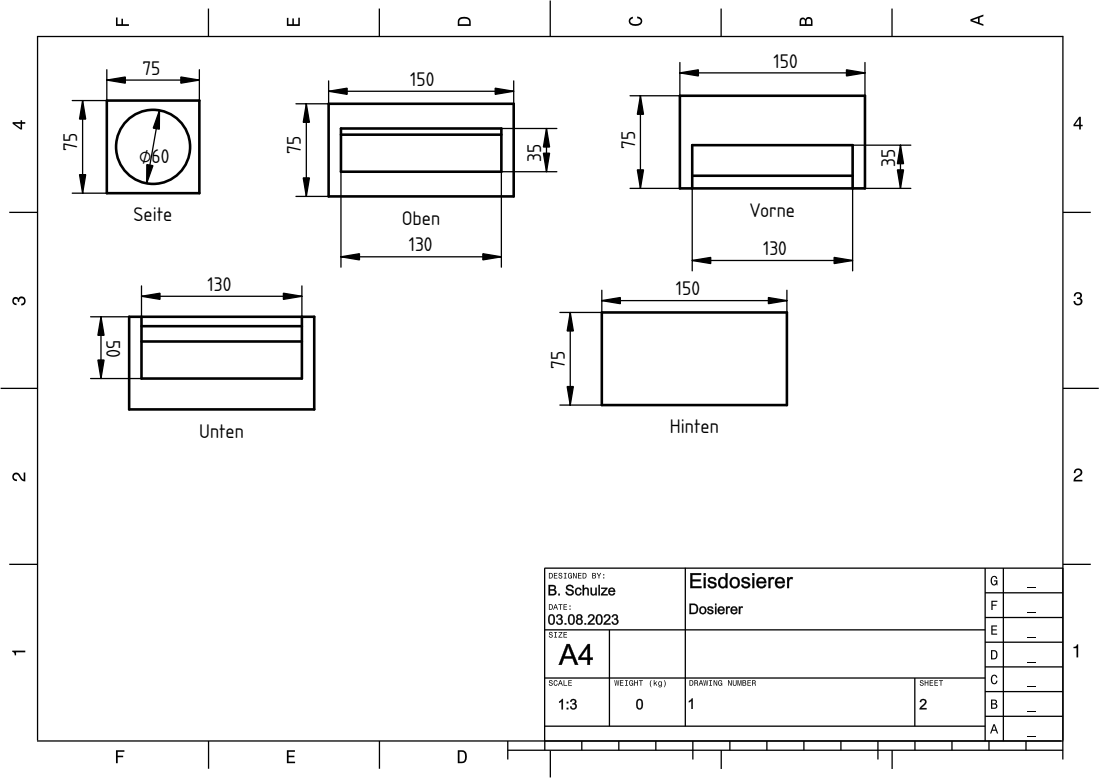
[picture p107: page 2]
eite; V orn; U nte; Hinte

0 132

# nitt Schnitt15

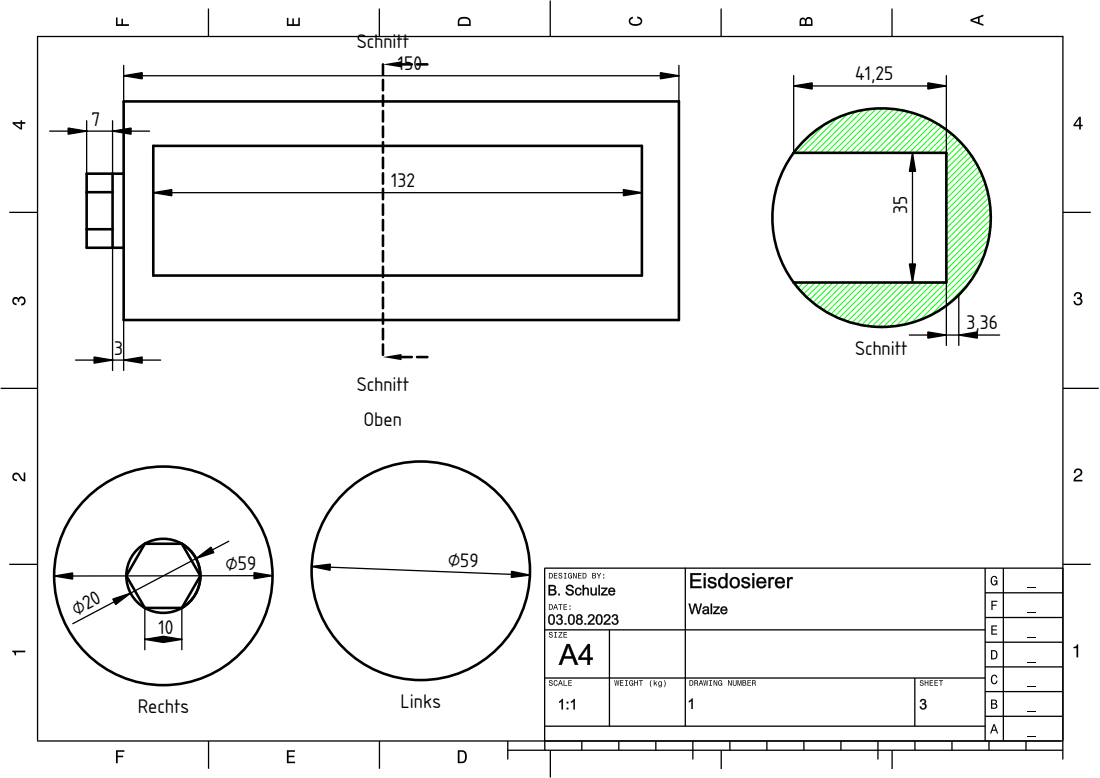
[picture p108: page 3]
echts; Sch; nitt³⁵; Lin

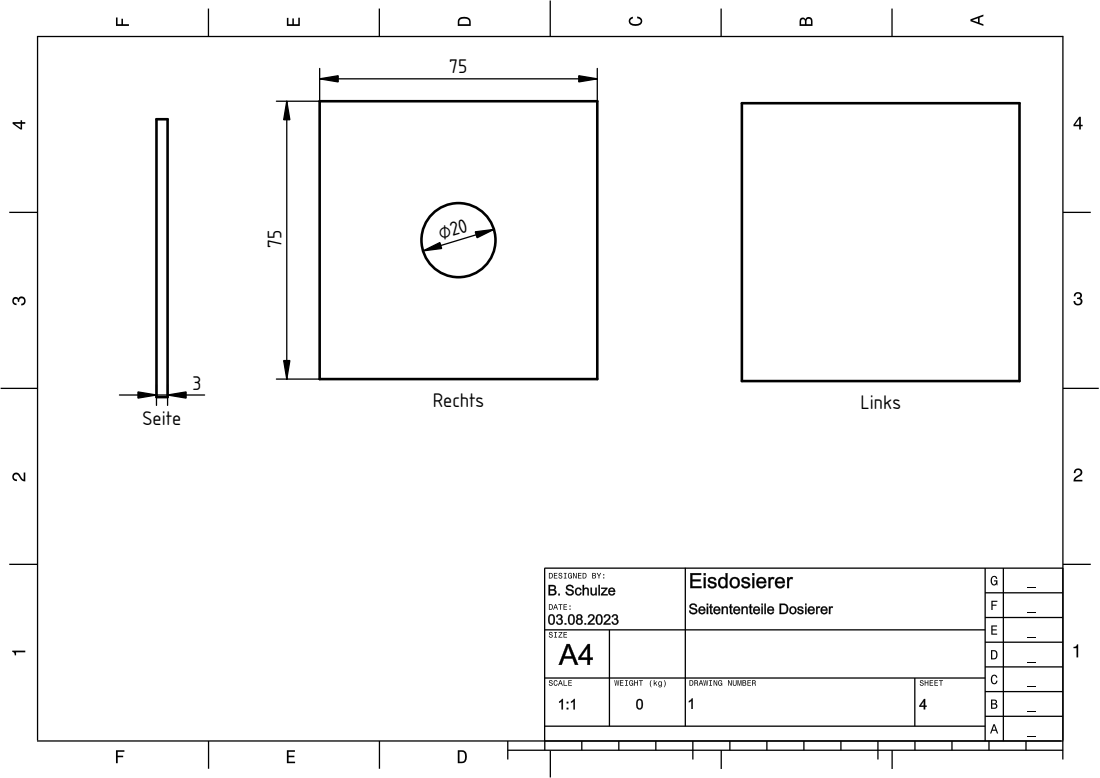
[picture p109: page 4]
echts; Lin; eite

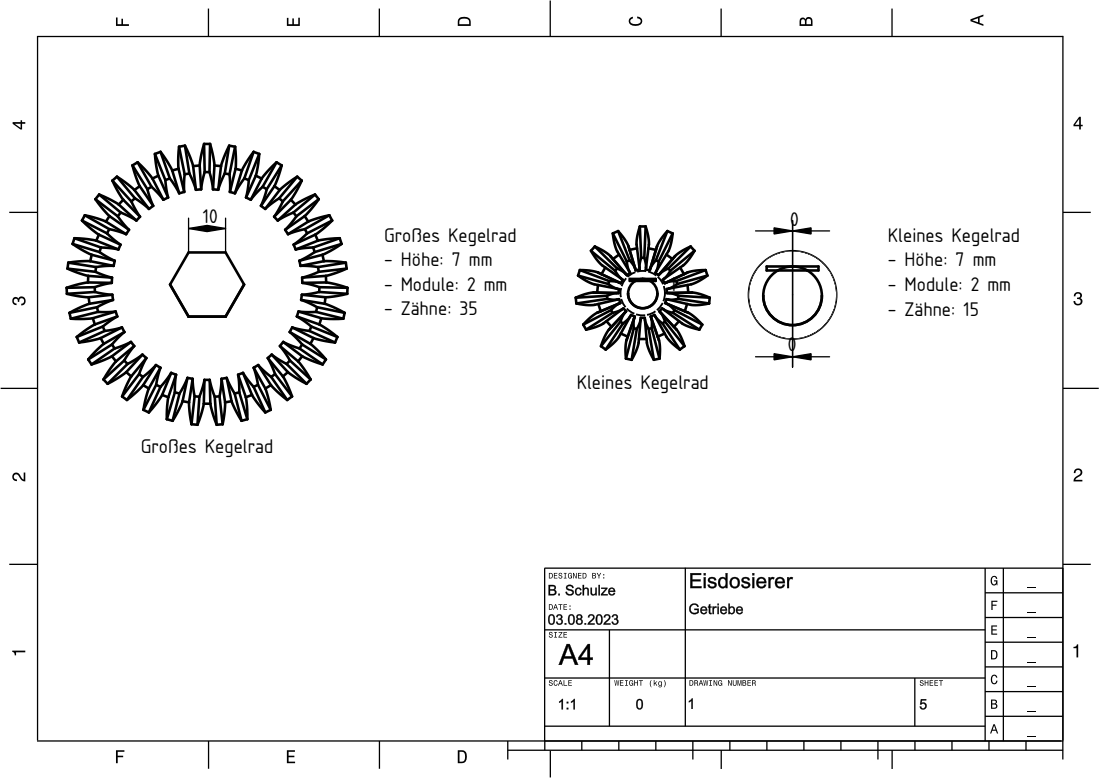
[picture p110: page 5]
Großes Kegelrad; Großes Kegelrad - Höhe: 7 mm; - Module: 2 mm - Zähne: 35; Kleines Kegelrad; Kleines Kegelrad - Höhe: 7 mm; - Module: 2 mm - Zähne: 15

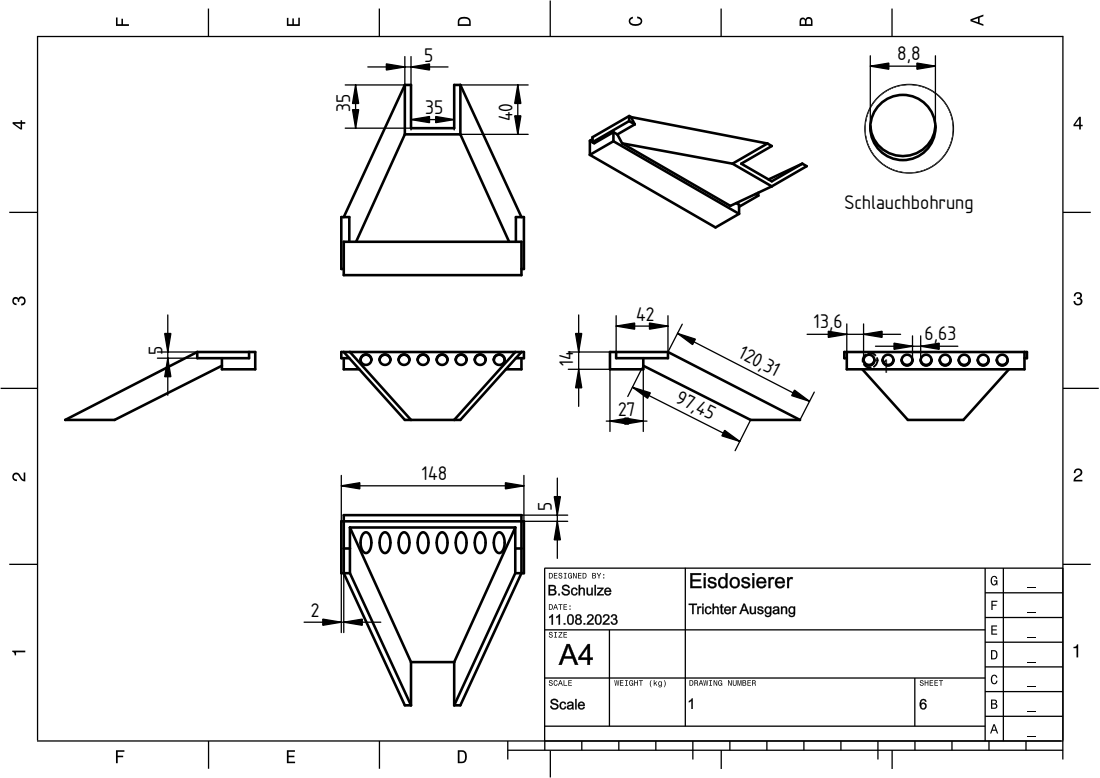
[picture p111: page 6]
Schlauchbohrung

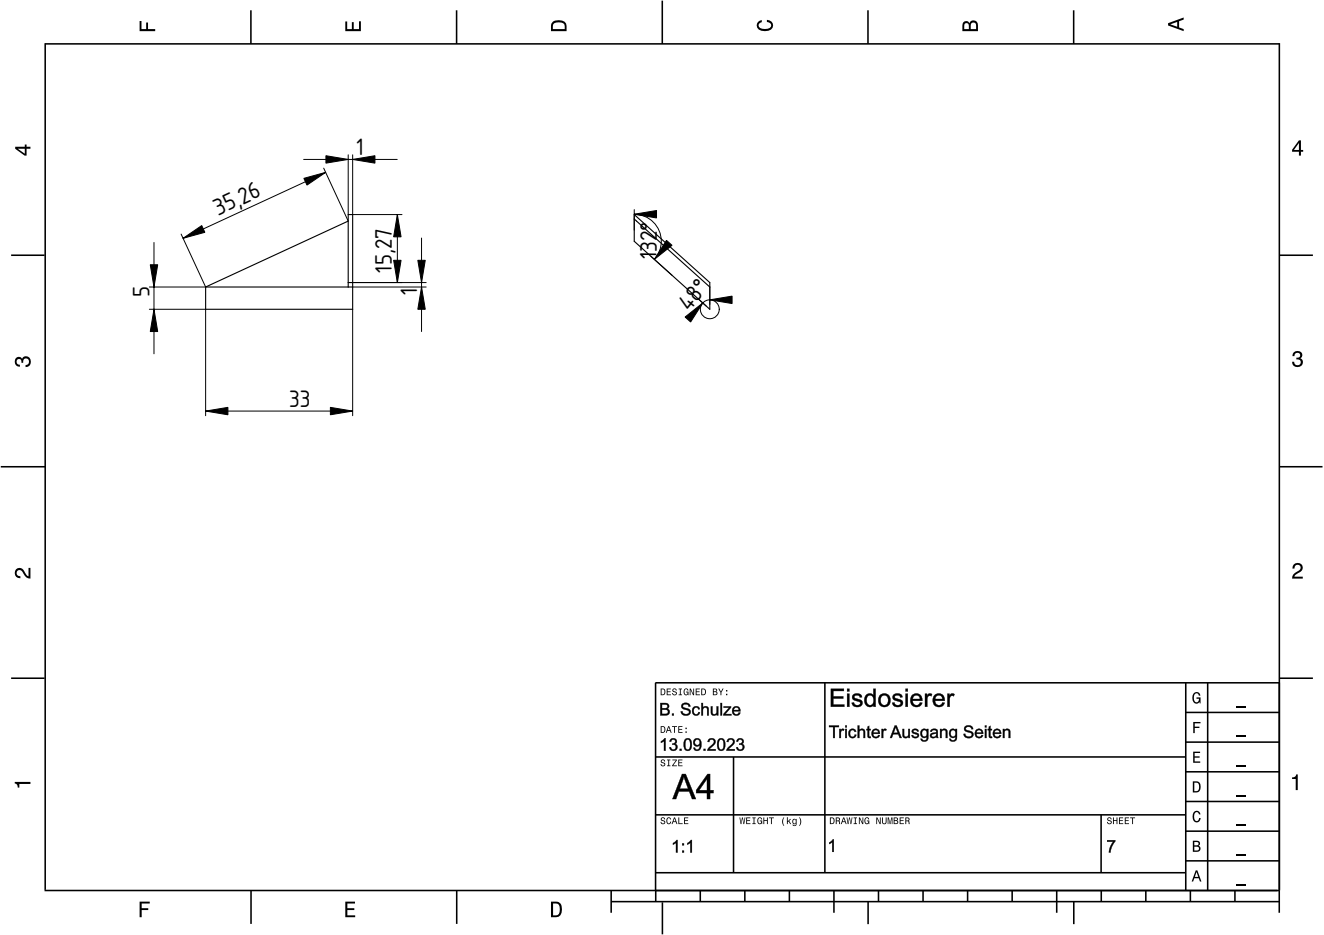
[picture p112: page 7]

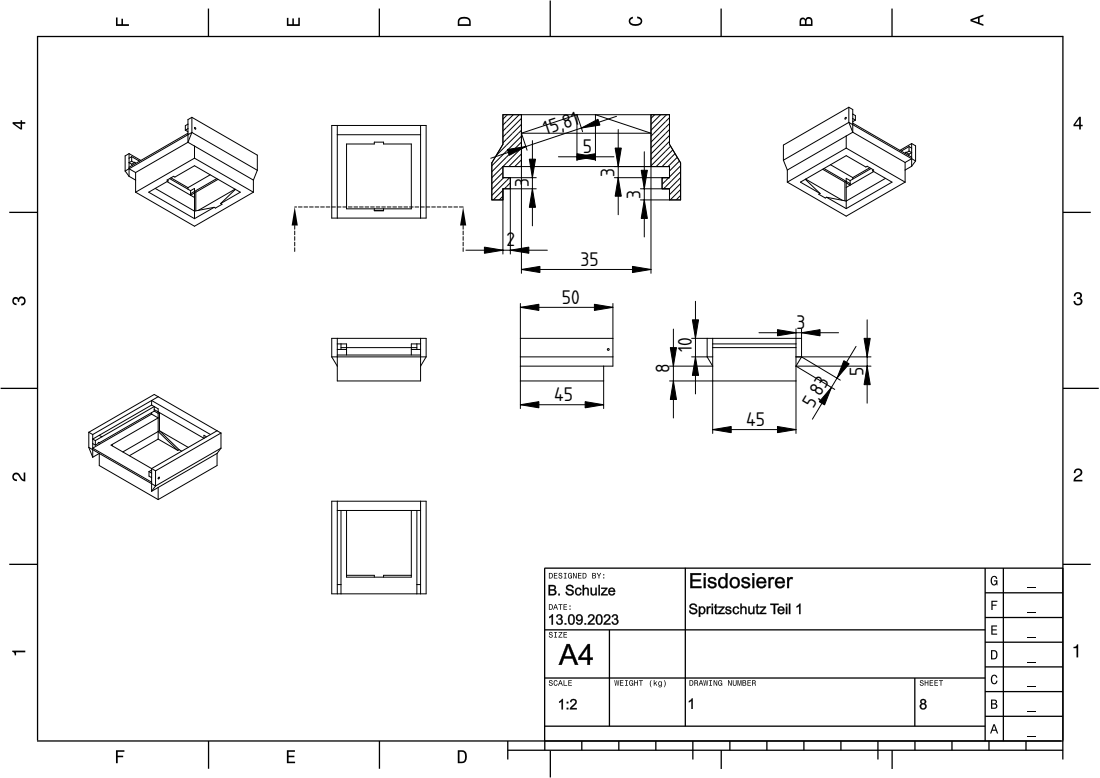
[picture p113: page 8]

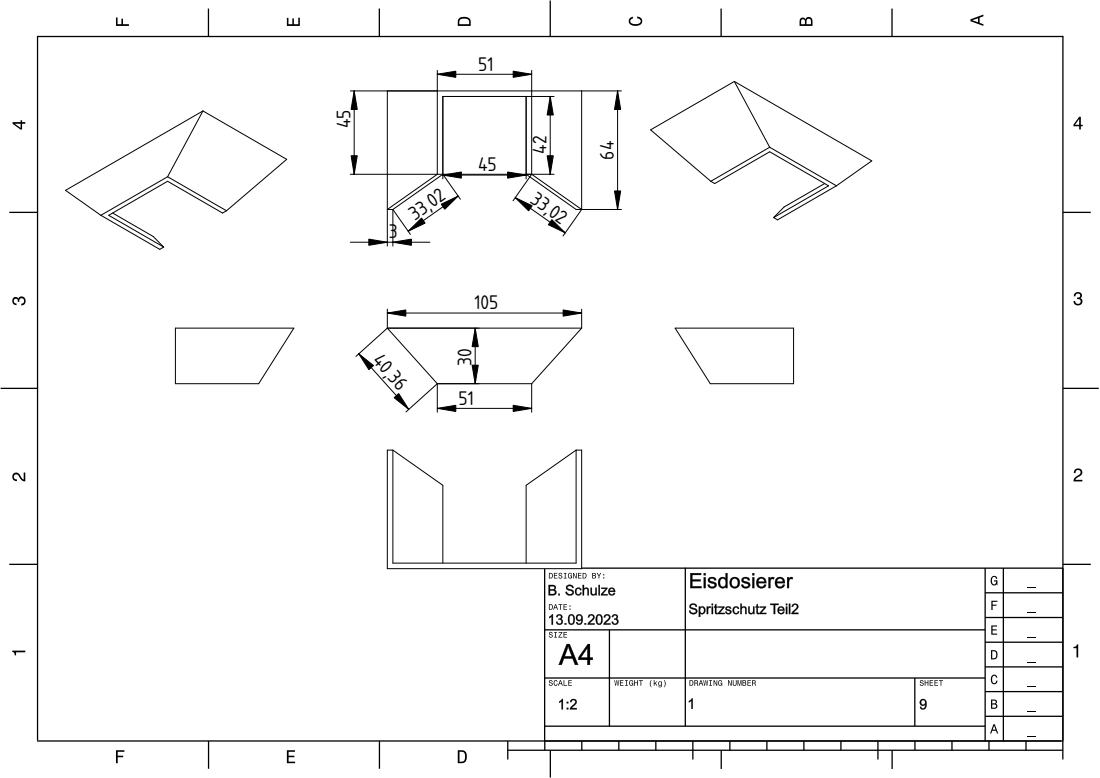
[picture p114: page 9]
