MaxVinzens/Cocktail-Mix-Maschine-V2/Doku/Abb.3_Verkleidung_Skizze.pdf

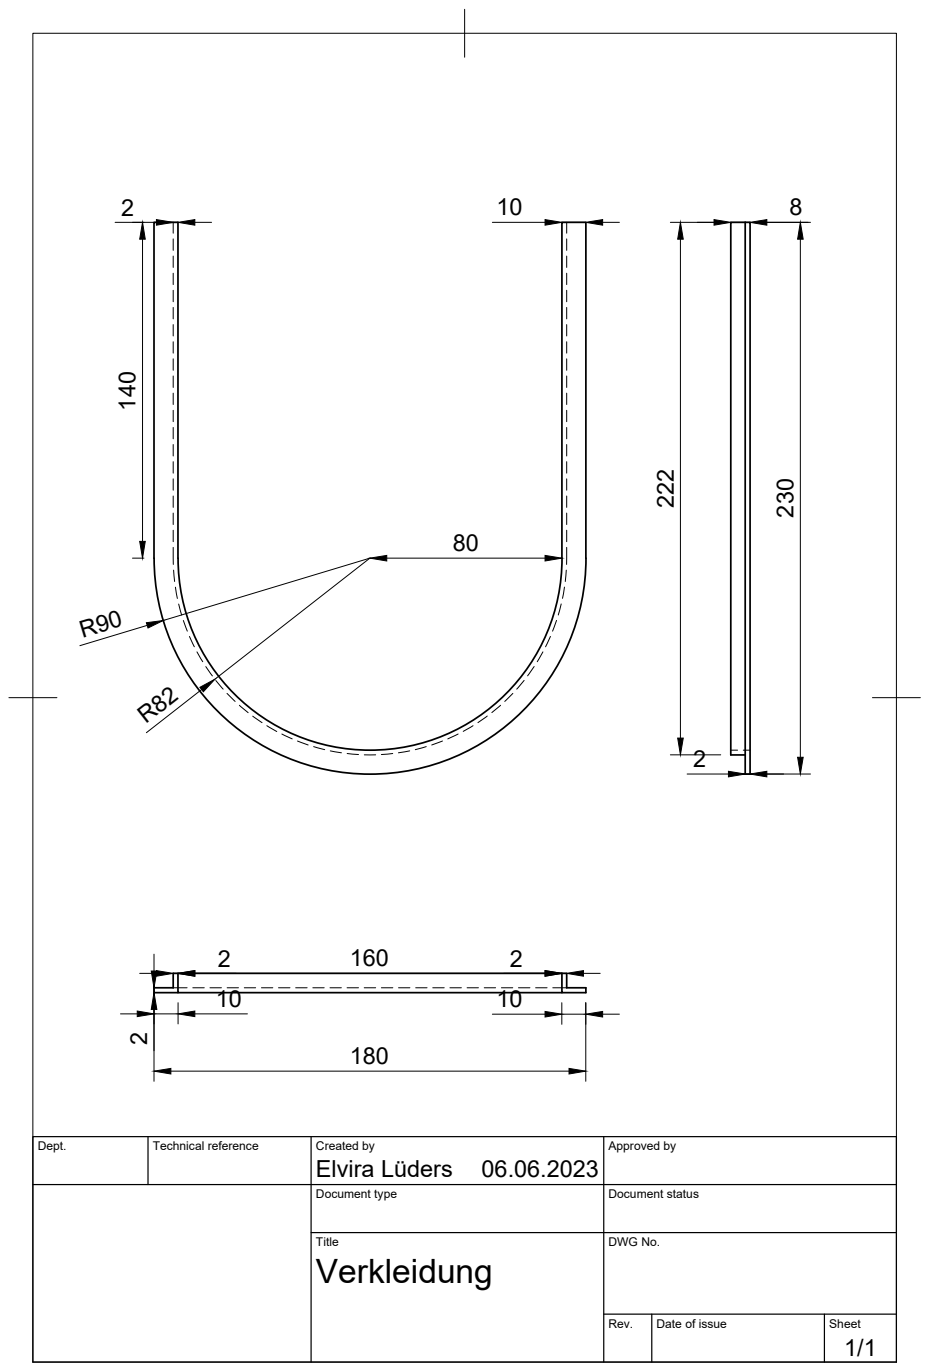
[picture p118: page 1]
Elvira Lüders 140

Dept. | Technical reference | Created by 06.06.2023 | Approved by

Document type | Document status

Title Verkleidung | DWG No.

Rev. | Date of issue | Sheet 1/1
