MaxVinzens/Cocktail-Mix-Maschine-V2/Doku/Abb.6_Becherhalterung_Skizze.pdf

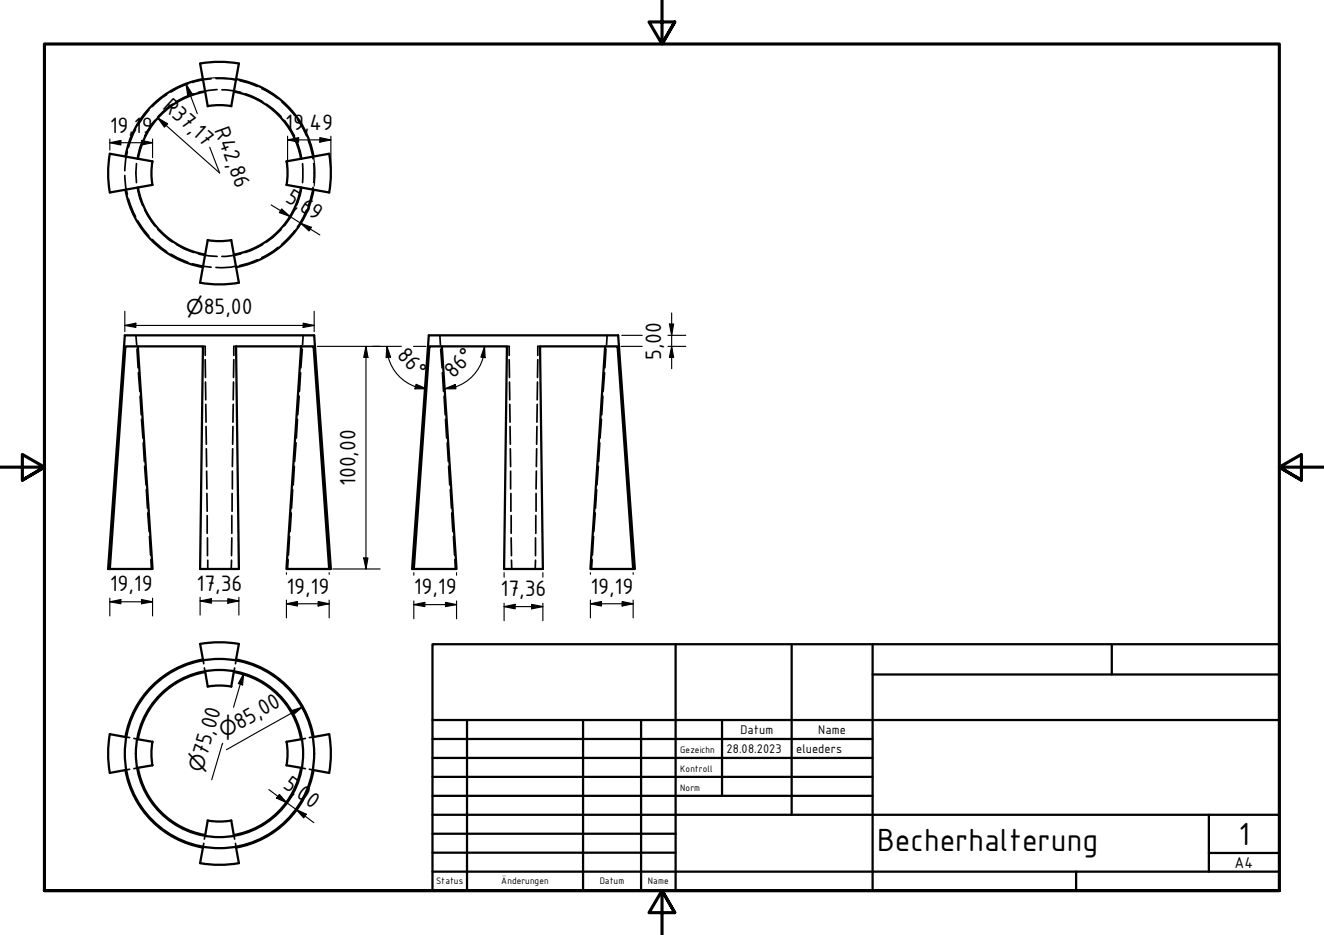
[picture p119: page 1]

Datum | Name

Gezeichn | 28.08.2023 | elueders

Kontroll

Norm
